dudgeon/count-fidget/procurement/q4/drill-report-Q4.txt

Drill report for click-counter-Q4.kicad_pcb
Created on 2026-09-24T20:55:30

Copper Layer Stackup:
    =============================================================
    L1 :  F.Cu                      front
    L2 :  B.Cu                      back

Drill file 'click-counter-Q4-PTH.drl' contains
    plated through holes:
    =============================================================
    T1  0.300mm  0.0118"  (79 holes))
    T2  0.600mm  0.0236"  (4 holes)  (with 4 slots)
    T3  1.020mm  0.0402"  (7 holes))
    T4  1.500mm  0.0591"  (4 holes))

    Total plated holes count 94

Drill file 'click-counter-Q4-NPTH.drl' contains
    unplated through holes:
    =============================================================
    T1  0.650mm  0.0256"  (2 holes))
    T2  2.200mm  0.0866"  (4 holes))
    T3  3.950mm  0.1555"  (2 holes))

    Total unplated holes count 8
