dudgeon/count-fidget/LOCAL_SESSION_PROMPT.md

Continue my Count Fidget project from https://github.com/dudgeon/count-fidget in this local session.

Clone/open the repo, read AGENTS.md, PROJECT.md and HANDOFF.md, then follow the handoff. It contains the product requirements, design files, decision history, vendor conversations, exact upload files and unresolved engineering issues. Do not restart or ask me to repeat the requirements.

First verify that you can actually control the local browser. Then complete the already-authorized website submissions to PCBWay and JLCPCB and obtain itemized quotes for 5 and 10 fully assembled/programmed/tested units, including the prepared rechargeable battery harness and delivery. Record real upload/submission evidence. Check existing replies and the old scheduled cloud follow-up to avoid duplicate actions.

Do not spend money, preorder chargeable parts or release manufacture until I approve a concrete order. The Q1 design is a quotation prototype; preserve the documented qualification gaps and keep moving on the work you can complete.
