dudgeon/count-fidget/docs/REVIEW-Q5-2026-09-25.md

# Q5 engineering review — 25 September 2026

**Start here for Q5.** Q5 is a coordinated revision of the frozen Q4 candidate. It resolves the ten findings filed from the Q4 simulation review ([issues #2–#9, #12, #13](https://github.com/dudgeon/count-fidget/issues?q=is%3Aissue)) and the owner's requests of 25 September:
- soft power on the COUNT key with automatic power-off;
- a battery gauge, low-battery warning and storage cut-off;
- charge status;
- a reachable hardware reset;
- new key logic (increment wins; reset needs a deliberate hold);
- a shrunk enclosure;
- a BOM of JLC inventory parts only.

Q1–Q4 files are unchanged.

The design is **locked** as of the evening of 25 September (see [Design lock](#design-lock--25-september-evening)). JLCPCB quoting was then authorized for two variants only:
- variant A: JLC does all SMT and the user solders the display;
- variant B: JLC assembles everything.

The result is in [JLC-QUOTE-Q5](../procurement/q5/JLC-QUOTE-Q5.md). No order, payment, allocation, manufacturing release or other-vendor contact is authorized. Everything here is design-file, host-model, emulator and CAD evidence. **Nothing has been built or measured.**

Related documents: [Q5 power design](q5-power-design.md), [Q5 firmware and home programming](q5-firmware.md), [enclosure and assembly](../mechanical/q5/README.md), [build workflow](build-and-verify.md#active-q5-engineering-workflow), [Q4 simulation review that raised the issues](REVIEW-Q4-simulation-2026-09-25.md).

## What Q5 is

- **Unchanged from Q4:**
  - STM32L072CBT6 with ROM USB DFU;
  - FM25V02A SPI FRAM with the same 96-slot journal (a Q4 FRAM image reads unchanged);
  - HS96L01W4S03 SPI OLED module;
  - BQ25185 charger, BQ29700 protector, TLV767 3.2 V rail;
  - two-layer 42 × 54 mm board and the same four mounting holes, now **1.6 mm** thick (required by the hot-swap sockets).
- **Parts count:** **95 references: 81 fitted (80 vendor SMT + DS1) and 14 PCB features**, 41 exact MPNs.
  - The key switches are no longer soldered. SW1/SW2 are vendor-placed MX hot-swap sockets, and the loose clicky switches K1/K2 press into them.
- **Home completion:**
  - variant A: 14 joints (the display header);
  - variant B: none (JLC fits DS1).
- **Offboard items:** reduced to the user-supplied LIR2032 cell.

## Fix order and why

Each fix was placed so that nothing done earlier had to be redone:

1. **Architecture/netlist decisions first** (#12, #13, #8, #5): power latch, cell holder + onboard NTC, battery sense, charger status, QOD. These change pins, so firmware and layout depend on them.
2. **Firmware** against the new pin contract:
   - boot capture gate (#2);
   - key semantics and DFU safety (#3 and the owner's reset rule);
   - option-byte provisioning (#6);
   - responsiveness (#7);
   - power-off, gauge and cut-off (#12, #9.4);
   - PVD wording (#9.1).
3. **Instruction-level emulation** of the actual ELF on a Q5 board model, before any layout work, so behavioural bugs were found cheaply. Four firmware defects were found and fixed here: the mV overflow, the label priority, the USB-during-LO cancel, and release-loop flapping.
4. **PCB placement, routing, ERC/DRC** once the netlist was final.
5. **Enclosure** from the final routed board (#4, pack-bay removal, keycaps, reset pinhole, shrink).
6. **Stock screen and exports** bound to the final model hash.
7. **Documents and issues.**

## Design lock — 25 September (evening)

Three independent reviews ran against the first Q5 candidate: hardware/DFM, firmware, and mechanical/quote. Their findings were fixed before the lock:

| Area | Finding | Fix |
|---|---|---|
| Latch | A short COUNT press could release U7 before PB2 took over; the power-on press could be lost | The reset handler drives PB2 first. C40 on SYS_ON bridges the gap (4.7 nF at the lock, 10 nF from 26 Sep: 9.9 ms). The boot scan captures edges. R38 isolates the VBUS path. Minimum press 10.5 ms typ / 16.3 ms allowance with 10 nF. Emulator B5/B6 |
| Firmware | After a DFU leave, ROM leftovers (VTOR, USB, SYSCFG) hung the app | `startup.c` detects leftovers and resets. Emulator D5 |
| Firmware | ADC read without VREFINT ready or LFMEN; option provisioning loop; key releases counted as activity | Fixed per [q5-firmware](q5-firmware.md) |
| Assembly | The two MX switches needed home through-hole soldering, and JLC has no stocked clicky 5-pin MX switch | **HanElectricity CPG151101S11-16 hot-swap sockets (C41430893)**, vendor SMT on the bottom. The clicky CPG151101D13 switches clip into the printed plate and press in. A soft-tactile JLC switch was rejected because the click is central per the user research. The sockets need a **1.6 mm** PCB |
| BOM cost | 10 generic passive/FET types were Extended parts ($3.07 feeder fee each) | Swapped to JLC Basic equivalents with the same value, package and rating (0.1 % dividers, 10 µF/2.2 µF and BAT54C unchanged): 25 Extended types remain |
| Silkscreen/DFM | Strokes < 0.15 mm, BT1 inner silk, BT1 paste, J1 shield ring | All raised to JLC minimums; BT1 +/− marks added |
| Enclosure | Keycap datum, screw engagement, boss clipping, USB rib | M2 × 6 self-tapping (C357360) with 3.4 mm engagement, keycaps re-datumed on the socket; body **47.2 × 59.2 × 16.8 mm** |

After the lock the whole chain was re-run on the final sources:
- placement and routing (deterministic Freerouting);
- fresh ERC/DRC/parity;
- the verifier and its corruption tests;
- stock screen and exports;
- enclosure;
- emulator and flasher tests.

The home flashing tool for macOS is `tools/clicker-flash/` (Claude skill `flash-clickers`). It is tested against a dfu-util emulator and against real dfu-util argument handling with no device attached. It has not been used on a physical board.

## Basic-part review — 26 September

Every JLC Extended part type adds a $3.07 feeder fee to each order. At the 2–5-board first-article quantity that was $77 of fixed cost, about $15–38 per board. The owner asked that every Extended part earn its place.

Nine types moved to JLC Basic parts; the circuit was re-derived where the value changed:

| Part | Was (Extended) | Now (Basic) | Effect |
|---|---|---|---|
| R4 ISET | 16.5k | 18k (C25810) | Charge current 300/R = **16.7 mA** (was 18.2 mA); 0.37C of a 45 mAh cell. Termination 1.67 mA, still < 0.05C |
| R10/R11/R12/R13 temperature window | 57.6k/115k/24.3k/16.2k | **56k/82k/18k/12k** | Nominal B3380 NTC enable window **7.26–35.83 °C** (was 7.49–35.92 °C) |
| R32 memory-rail resistor | 68 Ω | 75 Ω (C4275) | 10 % slower VFRAM ramps (more margin on the FM25V02A slew minima); drop at 3 mA 0.225 V, VFRAM ≥ 2.93 V |
| Q1/Q2 protection FETs | DMN2056U-13 | **AO3400A** (C20917) | Same SOT-23 G/S/D; 30 V; ≤ 48 mΩ at VGS 2.5 V, so the 24.8 mA OCD bound is unchanged. LCSC pin names checked |
| C1/C3/C5 | Murata 2.2 µF 25 V X7R | Samsung CL21A225KBQNNNE 2.2 µF **50 V** X5R | Same 0805 land; more effective capacitance at 5 V |
| C2/C6/C30 | Murata 10 µF 25 V X5R | Murata GRM21BR61H106KE43L 10 µF **50 V** X5R | Same 0805 land; more effective capacitance. C30 ≥ 6.8 µF remains a first-article measurement. Slightly more SYS capacitance at cold insertion; that counterexample was already retained, and USB-first insertion still applies |

Result: **16 Extended types (was 25), about $28 less per order.** The re-verified chain passes: ERC, fresh DRC/parity on the unchanged routing, stock 42/42, exports, the JLC footprint fit (no mirror or pad-order error) and the power and latch checks.

The 16 remaining Extended types, and why each stays (no Basic equivalent without a redesign):

| Part | Why it stays |
|---|---|
| STM32L072CBT6 | MCU with ROM USB DFU, the home-flashing path |
| FM25V02A FRAM | Count journal with unlimited endurance and instant, brownout-safe writes |
| BQ25185 | Li-ion charger with power path and status pins |
| BQ29700 | Li-ion cell protection (safety) |
| TLV76701 LDO | Adjustable 3.2 V rail kept below the 3.3 V logic and FRAM limits |
| 150k 0.1 % (R30/R36/R37), 49.9k 0.1 % (R31) | The LDO set point and the 0.26 % ADC margin that separates USB from a full cell |
| TPS22917 (U6/U7) | Soft-power latch and display power switch |
| TLV7012 | Charge-temperature window comparator |
| NCP18XH103F03RB NTC | No Basic 10k NTC; the window is designed around its B3380 curve |
| R9 3.3 Ω | Sets the ~25 mA protection trip; no Basic 3.3 Ω exists, and 2.2/4.7 Ω would move the trip to ~37 or ~17 mA |
| BAT54C | Power-latch OR diode; replacing it with two Basic diodes would need re-layout |
| USBLC6-2SC6 | USB ESD protection; no Basic equivalent |
| USB4105 USB-C | The enclosure is designed around it |
| CR2032-BS-6-1 holder, CPG151101S11 hot-swap sockets | Unique mechanical parts |

## First-order de-risking — 26 September

Before the first paid order, the owner asked for more certainty. Three independent checks ran on the locked design:

| Check | Result | Evidence |
|---|---|---|
| **Datasheet pinout audit** of every active and polarised part (MCU pins and SPI alternate functions, charger, LDO, protector, comparator, switches, FRAM, ESD, diodes, FETs, USB-C, holder, sockets, display module) | **No pin-assignment errors.** The standard footprints are pad-for-pad identical to the official KiCad library, and the custom ones match the vendor drawings. | [pinout audit](first-order-derisk/pinout-audit-2026-09-26.md) |
| **Footprints against JLC's own EasyEDA footprints** (all 43 LCSC parts) | **No pad-order or mirror errors.** The raw KiCad CPL, however, would show ~15 polarised parts with the wrong pin 1 in JLC's preview, and SW1/SW2, J1 and DS1 offset. JLC-corrected CPLs were generated, and a preview checklist is in [JLC-QUOTE-Q5](../procurement/q5/JLC-QUOTE-Q5.md). | [footprint check](../scripts/q5_jlc_footprint_check/REPORT.md) |
| **Dead-on-arrival review** of the power-up paths, back-feeding, programming and latch failure modes | **No defect likely to leave a board dead or unrecoverable.** USB-only power-up, DFU entry (crystal-less, BOOT0 only) and the SWD fallback pads are confirmed. | this section |
| **Latch transient** (behavioural ngspice, bouncing contacts, 54 corners) | 120/120 bouncing presses latched. The worst-case minimum press is 14.5 ms with 10 nF (20.0 ms with 4.7 nF). USB alone turns the board on at every corner. | [q5-latch-spice](../simulation/q5-latch-spice/README.md) |

The findings led to these changes, all re-verified through the full chain: model, ERC, re-route, DRC/parity, verifier corruptions, emulator, stock, exports and enclosure.
- **R39 1k + C9:** filters U5's supply. U5 is a TLV7012 with a 6 V absolute maximum, and it was on raw VBUS, exposed to USB hot-plug ringing.
- **C40 4.7 → 10 nF:** doubles the bounce bridge and cuts the minimum latch press to 10.5 ms typical.
- **JLC-corrected placement files** plus a preview checklist.
- **Flasher and skill:** a clicker left in DFU mode must be reset with the pinhole *before* unplugging. The ROM's D+ pull-up back-feeds VBUS through the USBLC6 and holds the latch on, draining the cell.
- **Doc corrections:** the SSD1315 VBAT absolute maximum is 6 V (4.5 V is the recommended maximum), and the BQ25185 battery UVLO (~3.0 V) comes before the protector's 2.8 V.

Accepted and documented rather than changed:
- **Display module at 3.15–3.26 V.** The module's external input is specified at 3–5 V. The 3.5–4.2 V figure is the controller's internal pump input, and the module's internal power tree is undocumented. First-article test E1.
- **STAT pull-ups.** The MCU's internal ~40 kΩ is outside TI's 1–20 kΩ recommendation, but it is adequate for a static status read.
- **VDDA.** It has 100 nF only; ST also recommends 1 µF. The 10 µF bulk capacitor sits on the same rail.
- **No watchdog.** Firmware can be updated after assembly.

Recovery routes if something is wrong on the first boards:
- **SWD:** TP3 SWDIO, TP4 SWCLK, TP11 NRST and TP1/TP2 accept a standard ST-Link.
- **Latch control fails:** bridging TP13 (SYS_ON) to TP6 (SYS) holds the board on.
- **Stuck in DFU:** the pinhole resets it.

## Resolution by issue

| Issue | Q5 resolution | Evidence | Remaining physical gate |
|---|---|---|---|
| [#2](https://github.com/dudgeon/count-fidget/issues/2) boot ERR after journal wrap | Button capture starts only after the journal load. Faster boot: FLASH latency 0, CS guard 110 loops, nibble CRC-32 table. | Emulated boot drains the queue at 207 ms with all 96 slots valid; no sample dropped; host CRC equivalence over 20,000 records | Boot timing on silicon |
| [#3](https://github.com/dudgeon/count-fidget/issues/3) DFU entry zeroes count | A reset commits only on **release** after a completed ≥ 2 s hold. A key held at MCU start is a level, not a press. On battery, NRST is a power cycle. | Emulator D1–D4 preserve the count in both DFU entry orders | Real DFU enumeration |
| Owner key rule | Both keys → **increment wins**, and the reset is cancelled. Reset needs a **2 s hold** (RST shown) and a release before 10 s. | 826 host key-hold cases; emulator K2, K3, K5–K7 | Contact bounce on real switches |
| [#4](https://github.com/dudgeon/count-fidget/issues/4) USB plug can't mate | 13.4 × 7.2 mm opening on the receptacle axis, cut through to the receptacle face; checked against a USB-IF maximum overmold | Fit report: USB mouth 2.0 mm from outer wall, no intersections | Real cables, both orientations |
| [#5](https://github.com/dudgeon/count-fidget/issues/5) 2–3 week battery life | Solved by #12: everything below SYS is off when idle; the regulator is kept | Off current 8.0 µA typ; emulated life 150–169 days on a shelf, 81–91 light, 42–48 moderate, 14–16 heavy | Measured off current and runtime |
| [#6](https://github.com/dudgeon/count-fidget/issues/6) blank board with factory option bytes | Firmware programs USER 0x807C once (BOR_LEV 0xC only; never RDP) and reloads. Any other mismatch shows **OPT**. | Emulator O1 (factory 0x8070 → provision → counts), O2 (OPT) | Option programming on silicon |
| [#7](https://github.com/dudgeon/count-fidget/issues/7) slow display | First frame in GDDRAM before AFh; partial redraw; 31-byte packets; no-divide glyph renderer; module powered during the journal scan | Press to digits 60–66 ms (Q4 200–225); USB Stop wake 0.34 s (Q4 0.77); off → lit 0.45 s | Optical response |
| [#8](https://github.com/dudgeon/count-fidget/issues/8) OLED supply | U6 QOD unconnected (SSD1315 §6.9.2). The display now runs only on a regulated ≥ 3.151 V rail because the 3.35 V cut-off precedes dropout. The supply choice is explained in the power document. | Netlist/ERC; emulator hard-reset cases note the floating supply | Module power tree, VBAT/pump/current, 200 × NRST |
| [#9](https://github.com/dudgeon/count-fidget/issues/9) minor findings | (1) PVD5 documented as best-effort only. (2) USB-first insertion cited to SLUSBU9I §8.4.1 in docs and assembly. (3) Cold-insertion counterexample retained; the latch keeps SYS_LOAD off at insertion. (4) **LO** label plus a 3.35 V cut-off, so there is no blind counting. | Emulator L1–L4; `simulation/q5-power` | Insertion on real cells; first-connection behaviour |
| [#12](https://github.com/dudgeon/count-fidget/issues/12) soft power | COUNT/SW1 switches SYS onto U7 ON; PB2 holds it; VBUS holds it via D4. The power-on press counts. 30 s auto-off on battery; Stop fallback with USB. | Emulator B1–B5, U1–U5, C4, H1/H2; latch press ≥ 10.5 ms typ / 16.3 ms allowance (C40 10 nF); ngspice 120/120 bouncing presses latched; inrush below the 24.8 mA minimum OCD over temperature | Latch timing with a bouncing contact; release behaviour |
| [#13](https://github.com/dudgeon/count-fidget/issues/13) JLC-inventory BOM | Pack/harness → vendor-soldered BT1 holder + onboard TH1. Keycaps printed. U5 moved to TLV7012DDFR (881 stock). All 41 MPNs pass a 10-board + spares screen. | `procurement/q5/stock.json`; offboard CSV = LIR2032 only | Signed-in JLC parts match for variants A/B ([estimate](../procurement/q5/JLC-QUOTE-Q5.md)) |

New in Q5 beyond the issues:
- **Charge status:** CHG while charging, full gauge when done, BAT on fault.
- **4-bar gauge.**
- **Reset pinhole:** a bottom opening reaches SW3 (NRST).

## Key and display behaviour (user-visible summary)

- **COUNT** (+ keycap) adds one; from off it powers on and that press counts. Held keys never repeat.
- **RESET** (○ keycap): hold 2 s until **RST** appears, then release (within 10 s) to zero. Pressing COUNT at any time cancels it.
- **Top-right:** 4-bar battery gauge. **LO** below ~3.55 V; below 3.35 V the count is saved and the board turns off. **CHG** while charging.
- **Auto-off:** 30 s after the last key on battery. With USB, the display sleeps and the MCU stops.
- **Label priority:** OPT > RST > ERR > MAX > LO > CHG/BAT.

## Validation record

| Scope | Evidence |
|---|---|
| Native schematic/PCB | Fresh KiCad 10.0.6: **ERC 0, DRC 0 violations, 0 unconnected, 0 parity**; 95 refs, 268 connected pins, 22 explicit NC pins ([binding](../verification/q5-validation.json)). 1,034 tracks, 121 vias, two GND pours, re-planned stitching vias ([gnd-stitch.json](../electronics/q5/gnd-stitch.json)); no same-net via closer than 0.1 mm to a land |
| Verifier corruption rejection | [42 of 42 rejected](../verification/q5-negative-tests.json) after a clean native baseline |
| Target build | Arm GNU 14.3.Rel1; 10,652 loaded bytes, 2,432 static RAM bytes, Bank 1 only, EEPROM and option bytes excluded ([manifest](../firmware/q5-stm32/build/build-manifest.json)); 13 image corruptions rejected ([image checks](../verification/q5-firmware-image-checks.json)) |
| Portable firmware models | [Full suite](../verification/q5-firmware-tests.json): 1,179,648 torn-word reboots, 256 bit corruptions, 7,072 button waveforms, 826 key-hold cases, 2,295 queue/storage schedules, 200 recovery interleavings, 350 FRAM faults, OLED transport faults at 80 positions, 1,527,742 rail corners, 1,301 battery-policy readings. [UBSan run](../verification/q5-firmware-sanitized-tests.json) (gcc; clang's UBSan runtime is not installed here) |
| Instruction-level emulation | 37 scenario records on the final ELF (SHA-256 below), **0 expectation failures** ([results](../simulation/q5-firmware-emulation/results/scenarios.json)); [energy model](../simulation/q5-firmware-emulation/results/energy-model.json) |
| Bounded power calculations | [result.json](../simulation/q5-power/result.json): latch, inrush, off current, ADC separation, cold insertion (counterexample retained), storage |
| Enclosure | [Fit report](../mechanical/q5/fit-report.json): five valid, manifold parts; zero static intersections; 162 poses / 18,387 sampled path tests with zero collisions; renders inspected |
| Stock and exports | 41/41 exact MPNs pass; lowest stock DMN2056U-13 189, HS96L01W4S03 524, TLV7012DDFR 881 (read-only public catalogue, unallocated). Exports in [procurement/q5](../procurement/q5/REVIEW-EXPORTS-Q5.md): variant A BOM/CPL (80 SMT rows) and variant B BOM/CPL (+ DS1, DS1H THT); loose parts; LIR2032 offboard |

- PCB SHA-256: `e78629ed361ff9f38c8ead58770e2dd60fc865461600456b503f6015345428df`.
- Firmware ELF SHA-256: `bb5a4a38aeeb41213e5f46c07e4a361e69b22f9b96742ebbff875b6083f58b03`.
- Gerber ZIP: 12 members, 134,522 bytes, SHA-256 `f9b9afe4ead8ebe9c9f7066926ef95a16f03e42750d92ad6f939462d12864230`.
- This ZIP was uploaded to JLC's public quote page for a price only. No RFQ was submitted, no cart was saved and nothing was ordered.

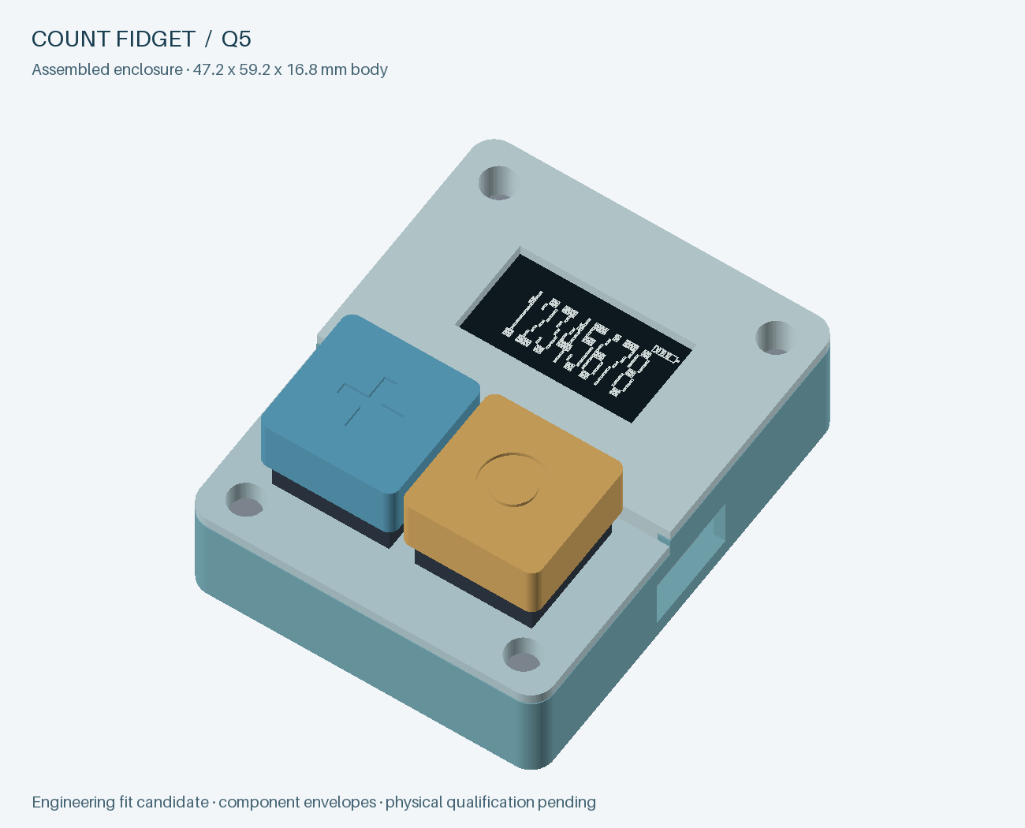
[picture p1: mechanical/q5/assembled-Q5.png]
Q5 CAD rendering


## Physical gates before an order can be released

The Q4 gates still apply: USB/target execution, supply/interface behaviour, charger/protector/temperature, count and display reliability, assembly and enclosure. Q5 adds or changes these:

1. **Power latch:** minimum press to latch with a real bouncing MX contact; clean U7 turn-off on PB2 release; USB unplug during Stop; the NRST power cycle on battery.
2. **Battery sense and status:** ADC accuracy through the 75 kΩ divider source; gauge thresholds against a real LIR2032 discharge under display load; STAT1/STAT2 behaviour in every charger state; measured ~8 µA off current.
3. **Cell and holder:** holder contact resistance and retention; insertion with USB present (BQ2970 first connection); the retained cold-insertion counterexample on real cells; TH1 thermal coupling to the cell.
4. **Display supply (#8):** module power tree; VBAT, pump, readability and current at 3.15–3.26 V; 200 × NRST with the display on.
5. **Enclosure:** real USB-C cables in both orientations; printed keycap cross-socket fit and travel; pinhole access to SW3; load supports; cell replacement.
6. **Process:** BT1, J1 and hot-swap socket solder inspection; variant B acceptance of the stacked THT display. The PCB price was observed on JLC's quote page, and PCBA is estimated from published fees; the parts-matched PCBA quote needs the owner's signed-in upload ([JLC-QUOTE-Q5](../procurement/q5/JLC-QUOTE-Q5.md)).

The full first-article procedure is [q5-first-article-test-plan.md](q5-first-article-test-plan.md).

**No whole-board simulation or physical working unit is claimed.** The evidence above supports building a first article when the owner authorises it. It does not replace these measurements.
