dudgeon/count-fidget/docs/q2-display-selection.md

# Q2 display recommendation

**Superseded by the user's explicit replacement requirement on 15 September 2026.** This is the historical Q2 decision. Continue with [Q3 display replacement](q3-display-selection.md); retaining DE188 did not satisfy support at both assemblers. Submitted Q2 files remain historical evidence.

Reviewed **2026-09-15**. **Retain the exact 3 V Display Elektronik DE188 for the corrected Q2 engineering baseline.** Correct its bias capacitors, frame timing and footprint; obtain an assembler's actual sourcing quotation before deciding to replace it. This is an engineering recommendation, not a purchasing or production approval.

The original eight digits, 35 × 13 mm envelope and 2–4-month runtime estimate were implementation assumptions, not user requirements. The user explicitly says the display choice was arbitrary. Even with those assumptions relaxed, the passive alternatives below do not have verified purchasable JLCPCB inventory. Reducing to four digits solely to resolve JLC sourcing therefore has no demonstrated benefit. The OLED and memory-LCD leads in [the earlier comparison](display-options-Q2.md) remain unqualified.

## Three concrete sourcing paths

All inventory and prices below are **indexed official distributor-page observations**, not live reservations, supplier commitments or complete assembly quotes. The stated crawl ages are part of the evidence. Prices are USD per component before assembly, fixtures, project freight and other commercial scope.

| Exact part | External sourcing evidence | Electrical/mechanical fit and assembly | Decision |
|---|---|---|---|
| **Display Elektronik DE 188-RU-30/7,5 (3 Volt)**; TME ordering name **DE 188-RU-30/7,5/V (3 VOLT)**, TME code **DE188-RU-30/7.5-3** | [TME](https://www.tme.com/us/en-us/details/de188-ru-30_7.5-3/lcd-digital-displays/display-elektronik/de-188-ru-30-7-5-v-3-volt/) reports **288**, MOQ/multiple **1**, **$3.60 single/$2.80 at ten**. Opened retrieval was crawled **five months ago**: useful source identity, weak evidence of today's quantity. No delivery date was obtained. | Reflective eight-digit glass, **34.9 × 13 mm**, 3 V AC, 1/4 multiplex, 20 leads. Existing MCU architecture and segment mapping remain useful. Through-hole assembly and glass support need approval. Use the exact **3 V Rev4 drawing**, not the 4 V variant. | **Preferred.** Least redesign while retaining the low-power architecture. TME is a sourcing lead for vendor confirmation, not an accepted PCBWay supply plan. |
| **Lumex LCD-S401M16KR**, JLC/LCSC **C17355221** | [DigiKey](https://www.digikey.com/en/products/detail/lumex-opto-components-inc/LCD-S401M16KR/7364561) reports **6,108**, quantity **1**, **$2.07 single/$1.484 at ten**, crawled **the previous day**. Listed manufacturer standard lead time **18 weeks** is not a quoted ship time for those stocked units. | [Manufacturer drawing](https://www.lumex.com/datasheet/files/LCD-S401M16KR.pdf): four reflective digits, **20.32 × 10.16 × 2.8 mm**, **3 V AC, 1/4 duty, 1/3 bias**, 12 leads. [JLC listing](https://jlcpcb.com/partdetail/Lumex-LCDS401M16KR/C17355221) identifies wave soldering but exposes no inventory figure; [LCSC](https://www.lcsc.com/product-image/C17355221.html) reports zero. | Credible smaller external-source fallback. Requires a new footprint, wiring/segment map, enclosure and count presentation beyond four digits. No demonstrated JLC inventory advantage. |
| **Varitronix VIM-878-DP-RC-S-LV**, JLC **C17231725** | [DigiKey](https://www.digikey.com/en/products/detail/varitronix/VIM-878-DP-RC-S-LV/1118605) reports **1,381**, quantity **1**, **$4.80 single/$3.556 at ten**, crawled **two weeks ago**. Its **20-week** manufacturer lead time likewise does not establish stocked-order delivery. | Eight 14-segment characters, reflective, **52 × 22 × 2.8 mm**, listed **3.3 V**. [Exact manufacturer drawing hosted by DigiKey](https://mm.digikey.com/Volume0/opasdata/d220001/medias/docus/693/VIM-878.pdf). [JLC](https://jlcpcb.com/partdetail/18360830-VIM_878_DP_RC_SLV/C17231725) shows **stock 0**, wave soldering and a required fixture. Exact MCU pin/drive compatibility and optical response have not been qualified. | Externally stocked eight-digit fallback, but its 52 mm glass exceeds the current 42 mm board width. Larger mechanical redesign and drive review bring no demonstrated JLC sourcing benefit. |

No assembler has provided a firm lead time or complete price for any of these sourcing paths. JLCPCB's representative suggested Global Sourcing preorder for DE188 and reported no stocked alternative to the originally narrow display request; see [vendor status](../procurement/vendor-status.md). That statement is not an exhaustive catalog search. Paid preorder remains unauthorized. PCBWay external sourcing still requires its acceptance, quantity, lead time and itemized price.

## Necessary DE188 work and remaining risk

1. **Bias hardware:** add the three nominal **100 nF** R13/R23/R33-to-ground reservoirs at MCU pins **7/8/9**. Retain the existing nominal 100 nF pump capacitor unless further review changes it. [TI datasheet §8.12.8.1](https://www.ti.com/lit/ds/symlink/msp430fr4133.pdf) and [family guide Figure 17-9](https://www.ti.com/lit/ug/slau445i/slau445i.pdf) support this correction.
2. **Timing:** use the separately verified **32 Hz** candidate. Its calculated REFO-tolerance range **30.88–33.12 Hz** fits the MCU and exact display recommendations. This does not measure the physical waveform or optical response.
3. **Footprint:** the [DE188 Rev4 drawing, p3](https://display-elektronik.de/filter/DE188-RU-30_75_3V.pdf) implies nominal **13.0 mm** lead-row centers, versus Q1's 13.5 mm. Confirm the interpretation and lead/hole tolerance stack; do not blindly shrink the existing drills. See [LCD audit](review-lcd-firmware-Q2.md).
4. **Response:** Rev4 p4 lists **440 ms total turn-on plus turn-off response**. That remains a meaningful fast-click visibility concern; changing frame frequency does not establish a faster glass response. The Lumex drawing does not supply a qualified optical-response comparison. Verify actual rapid counting, contrast, DC balance, temperature and current on a first article before accepting the display experience.

[NXP AN12579 §4](https://www.nxp.com/docs/en/application-note/AN12579.pdf) demonstrates the Lumex display in an active low-power development-board configuration at 7 µA. This supports a passive-LCD direction; it is not a bare-display specification, Count Fidget current measurement or runtime promise.

The separate Q2 native design implements the retained-display corrections and has its own verification and quote files. Q2 files are now uploaded to both vendors: PCBWay has a submission under review, and JLCPCB has a saved draft blocked at the unmatched required DE188 and stock shortages. Q1 remains historical and on engineering hold. See the [vendor ledger](../procurement/vendor-status.md) for current evidence. Charger, thermal, cell/protection, physical mechanical fit, target tests and other [release gaps](open-issues.md) remain open. File checks and a quote do not authorize spending or manufacture; concrete order approval remains required.
