dudgeon/count-fidget/docs/REVIEW-Q3-2026-09-22.md

# Q3 independent-review entry point — 22 September 2026

## Decision and boundaries

Commit the coordinated **two-layer OLED Q3 candidate** for another agent to review. Retain the exact circuit and part identities: fresh read-only research establishes a stock source for every fitted PCB MPN without speculative substitutions. This is a review candidate, **not a demonstrated working device or manufacturing release**. The new review strengthens the software evidence and identifies concrete conditional electrical failure scenarios; those scenarios remain open.

**No new quote submissions, uploads, draft changes or vendor messages are authorized.** The user paused them pending a separate explicit instruction. No purchases, paid preorders or manufacturing release occurred. The September15 RFQ is a frozen historical snapshot, not a new submission or a package containing this September22 review.

## What another reviewer should examine first

1. [Fresh hardware review and proposed remedies](review-Q3-2026-09-22-hardware.md) (a self-review by the power/layout author, alongside the separate September15 independent audit): I²C acknowledgement/rise-time margin, battery-insertion surge and OLED power budget. Challenge the model assumptions; do not treat its grid as guaranteed component limits.
2. [Fresh firmware adversary](review-Q3-2026-09-22-firmware.md): bounded tests execute the actual portable production modules, including torn writes and display errors. The MCU peripherals and analog supply are outside that model.
3. [Current exact-part inventory](../procurement/q3/stock-recheck-2026-09-22.json):40 MPNs available in JLC inventory and3 exact MPNs with independent distributor stock. This is not an all-JLC-stocked turnkey build.
4. [Home completion and cost options](home-completion-Q3-2026-09-22.md): shared programmer, optional home switches, USB programming tradeoffs and actual limits on claimed savings.
5. [Open issues](open-issues.md), [power circuit](q3-power-design.md), [original hardware review](review-hardware-Q3.md), [original firmware review](review-firmware-Q3.md) and [mechanical review](review-mechanical-Q3.md).

The board, schematic and all70 fitted references are under `electronics/q3/` and `procurement/q3/`. Firmware is `firmware/q3-oled/`. The MCU remains MSP430FR4133IG48R. The exact display is X087-2832TSWIG02-H14/C18723015, with a TPS63900 supply and gated pump input. Q1/Q2 remain separate historical revisions.

## Fresh stock result

Observed23:48–23:58 UTC on September22. All43 MPN records were checked against the actual70-reference design and their required ten-board quantities before attrition. Stock is neither reserved nor supplier allocation.

| Scope | Observed result | Limit |
|---|---|---|
| OLED C18723015 | JLC stock1,065; available1,052; minimum1 | Exact FPC assembly process still needs approval |
|40 of43 unique PCB MPNs | JLC explicitly showed sufficient available quantity for10 boards before attrition | MCU and comparator quantities are relatively tight; check allocation/attrition later |
|J1 USB4105-GF-A | JLC preorder/ordering restriction; LCSC out of stock; DigiKey129,457 exact parts | Distributor sourcing/consignment is not accepted vendor scope yet |
|Q1/Q2/Q6 DMN2056U-7 | JLC preorder/ordering restriction; LCSC out of stock; DigiKey57,542 exact parts | Need three per board plus eventual attrition |
|R13 RC0603FR-0716K2L | JLC preorder/ordering restriction; LCSC out of stock; DigiKey262,066 exact parts | Retain exact16.2k1% thermal-network identity |

Sources, observation times, minimum quantities and exact reference mappings are in the inventory record. DigiKey's cut-tape tiers start at1 for these three identities. No component was purchased or omitted. This establishes an exact-part sourcing path, not full support by both assembly vendors. The offboard custom welded cell/NTC pack remains a separate unapproved assembly; the43-MPN claim does not include it.

## Verification and its limits

| Check | Result | What it establishes |
|---|---|---|
|Q3 model/schematic/PCB/BOM/CPL and source-bound native evidence | Pass;82 references/features,218 connected pins,50 explicit NC,70 fitted components | Unchanged source agreement; existing native electrical/connectivity/parity results remain valid. One exact disclosed J1/SW2 courtyard projection remains |
|Negative checks |62 deliberately corrupted cases rejected on September22 | Checker rejects the tested identity, topology, geometry, report and provenance corruption |
|Firmware provenance | Source/output manifest passes; frozen ELF/HEX unchanged | Candidate images correspond to the recorded source/toolchain; original September15 independent exact rebuild remains evidence |
|New deterministic software model |2,359,296 torn-word cases;65,536 marker patterns;65,665 queue schedules/capacity cases;7,350 button waveforms;24 recovery-cut prefixes;5,441 OLED fault/sleep schedules pass | Bounded functional behavior of actual portable production code; not exhaustive states or electrical power-cut simulation |
|New hardware corner analysis | Conditional I²C and insertion-current counterexamples reproduced; RC result independently crosschecked numerically | Shows missing electrical guarantees. **Not a hardware pass** |
|Historical archive preservation |152 RFQ members match manifest and CRC; Q1/Q2 provenance checks pass | Preserved submitted/historical evidence |
|Mechanics | Existing source-bound four-part CAD result: valid solids/manifold meshes, zero modeled intersections | Simplified geometry/assembly sampling, not actual printing, material, harness or retention qualification |

No new native KiCad run was needed for this continuation because the final board/circuit and its bound inputs remain unchanged. The September22 binding recheck must not be described as newly executed native DRC/ERC. No new production-code bug was confirmed by the fresh bounded firmware tests.

### Concrete unresolved electrical questions

- **I²C:** the selected4.7k pull-ups require more sink current than the display's100µA output-low test establishes. A hypothetical6kΩ sink meets that table at100µA yet gives about1.68V acknowledgement with4.7k at3V, outside guaranteed MCU low recognition. It is a specification-consistent counterexample, not a measured OLED resistance. Weaker pull-ups alone do not establish compliance with the300ns rise limit and unknown bus capacitance.
- **Battery insertion:** a4.2V,20µF effective SYS,3.3Ω sense plus1Ω other-series-resistance model exceeds0.4V at the protector sense for about179.45µs, longer than its125µs minimum short-circuit delay. Actual cell impedance, capacitance, charger/protector gate slew and recovery are not established. TPS63900's10mA average input setting does not limit charging its input capacitor.
- **OLED operating budget:** the converter limit has no guaranteed min/max setting bound and sparse pixel current is unmeasured. Rail droop, pump startup and readability require proof under the intended load; a nominal efficiency calculation is not qualification.

Retain the cell/protection threshold,18.2mA charge stability, installed temperature sensing/fault response, capacitor effective values, sudden VDD collapse/FRAM, battery pack, actual assembly and runtime/mass gates. The firmware cannot preserve a newly detected volatile input-history gap if power disappears before its first marker write. The detailed reviews identify practical test and redesign branches; do not silently close those issues.

## Reproduce the review

From the repository root:

```sh
python3 scripts/verify_project.py
python3 scripts/verify_q3.py
python3 scripts/build_firmware_q3.py --verify-only
python3 scripts/test_verify_q3.py --full --bound
python3 scripts/test_q3_behavior_model.py
python3 scripts/analyze_q3_hardware_corners_20260922.py
```

The new software model needs a C11 host compiler; its result records the compiler, flags and input hashes. Existing negative checks use `/private/tmp` and need that scratch path on non-macOS hosts. See [build instructions](build-and-verify.md) for native tools if the engineering inputs change. Reusing an old binding after changing a bound input must fail.

Saved new evidence: `verification/q3-behavior-model-2026-09-22.json`, `verification/q3-hardware-corners-2026-09-22.json`, and `verification/q3-negative-recheck-2026-09-22.json`.

## Cost and USB programming decision

Two layers are already implemented. Retain one shared Spy-Bi-Wire programmer as the simplest current home-flashing path. Home soldering of the two switches is permissible if the actual savings justify it, but the observed manual-labor lines total only$5.06 per five-unit batch and include other work; the full$16.42 fixture is not necessarily avoidable. No savings quote is implied.

USB-C currently charges only. MSP430FR4133 has no native USB. Adding a USB-to-UART bridge would require bootloader-entry wiring and resolution of P1.0/P1.1 sharing with the buttons; a wrong bootloader password can erase information FRAM and the saved count. A native-USB MCU is a larger board/firmware/power redesign. The user's question does not select either change. Detailed constraints and primary references are in the firmware and home-completion notes.

The September15 JLC five-unit automatic total$255.86 and separate$3.28 depaneling remain historical incomplete pricing. No ten-unit Q3 total or complete delivered quote exists. Later email replies were read: JLC recognizes the OLED as an assembly component and said its wave-solder category appeared incorrect, referring it for correction; PCBWay requests one settled revision and warns that calculator prices are not final. No reply was sent.

## Rendering and immutable identities

[Actual assembled CAD rendering](../mechanical/q3/assembled-Q3.png), [STEP model](../mechanical/q3/enclosure-Q3.step).

- Board SHA-256: `b33b1e1d0c9e4d58c5642fc3f63faaa4e190092601f26103376537a5b12621fd`.
- Application HEX SHA-256: `b19f9e62fe9833ebb61fa75e94a7adef5664e51c7bcb7ffaa619a7c00bf910bf`.
- Historical September15 RFQ SHA-256: `4626d8ba64ef67d9bf5265399d6f6bf8e0d4ce9dda87d3656b5e5579aecef5ba` (4,031,548 bytes).

Next: independent review of this committed candidate, especially the three electrical questions and actual sourcing/assembly path. Resolve them as one coordinated revision before the user considers authorizing another quote. Do not restart the requirements interview or turn review completion into manufacturing approval.
