dudgeon/count-fidget/procurement/JLCPCB-IMPORT-ADAPTER-Q1.md

# JLCPCB Q1 import adapter

Prepared 2026-09-15 01:50:59 UTC. Quotation only; no design or manufacturing release.

## Observed import failure

During the local JLCPCB BOM import, the matching screen used descriptive Comment values such as COUNT and RESET and generic capacitor descriptions instead of the supplied Manufacturer Part Number column. This produced incorrect component matches. The earlier vendor screenshot also matched SW2 to E-Switch TL1220S1BBSG-RESET (C5798268), whereas the specified switch is Cherry MX1A-E1NW. Do not accept these automatic substitutions.

A first adapter import recognized the explicit catalog codes but still displayed the old descriptive values, including an incorrect LED match for R7 from the description 330. The importer appears to choose the last header containing Comment. The preserved-description header is therefore Source Label, with no Comment, Description or Value substring. This is an observed parser diagnosis, not a claim of successful matching.

The subsequent Source Label reimport displayed the exact MPN Comment values. This confirms the field-interpretation fix, while exact component matching and stock review remain unfinished. In particular, Q3 was still automatically mapped to a different manufacturer's part; U3 and DS1 remained unmatched. No complete quote resulted from this import.

## Adapter transformation

Use `BOM-JLCPCB-Q1.csv` with the unchanged `CPL-JLCPCB-Q1.csv` for this importer. It preserves every source row, row order and column. The only modified source field is Comment, set to the exact Manufacturer Part Number. The prior descriptive Comment is preserved in the appended Source Label column. The appended LCSC Part # column contains the verified exact catalog codes below for 11 references; all other code cells are blank.

`BOM-PCBA-Q1.csv` remains the controlling PCB BOM. The source BOM, full commercial BOM, CPL, Gerbers, firmware, electrical design and RFQ ZIP are unchanged. This adapter is a separately uploaded supplement and is not yet included in the RFQ archive.
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
