dudgeon/count-fidget/mechanical/exploded-cad.png

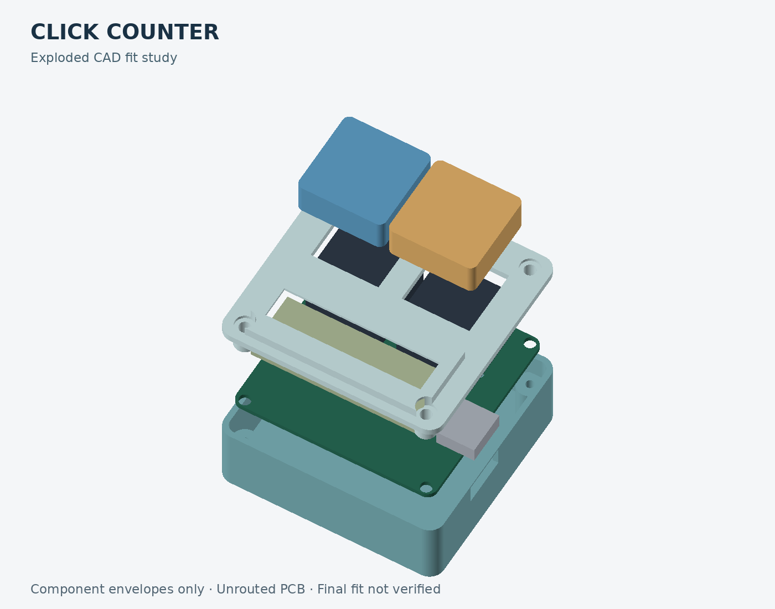
mechanical/exploded-cad.png
