dudgeon/count-fidget/mechanical/q2/battery-bay-Q2.png

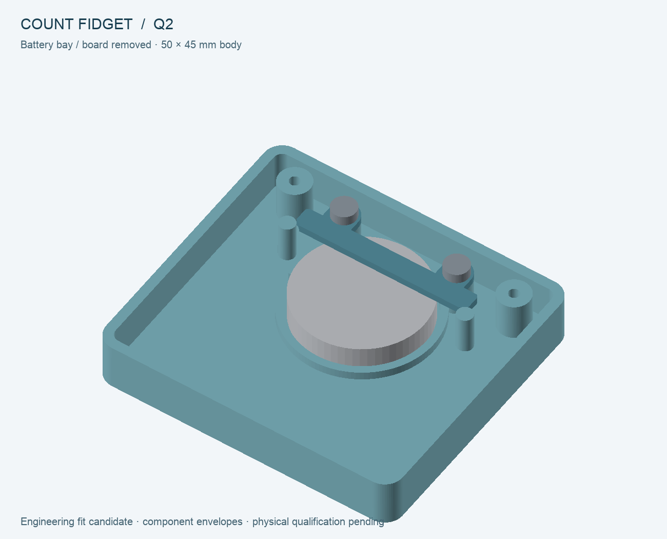
mechanical/q2/battery-bay-Q2.png
