dudgeon/count-fidget/mechanical/q2/exploded-Q2.png

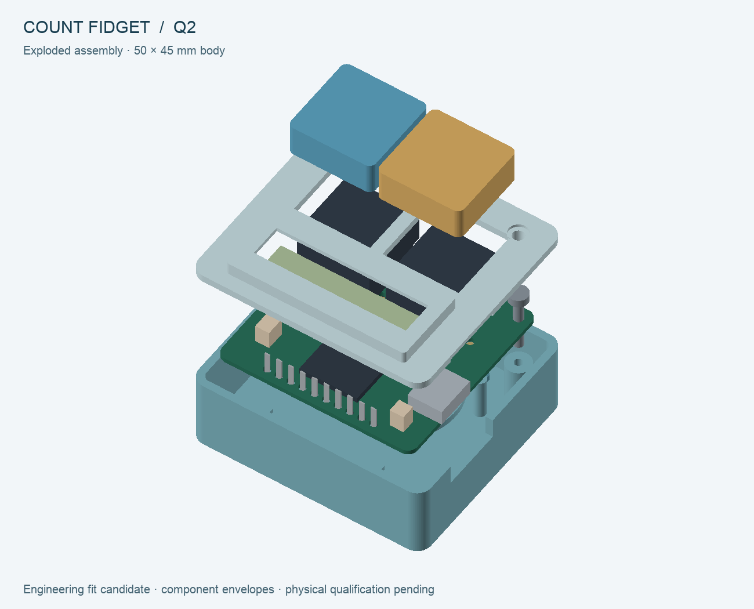
mechanical/q2/exploded-Q2.png
