dudgeon/count-fidget/mechanical/q2/interior-Q2.png

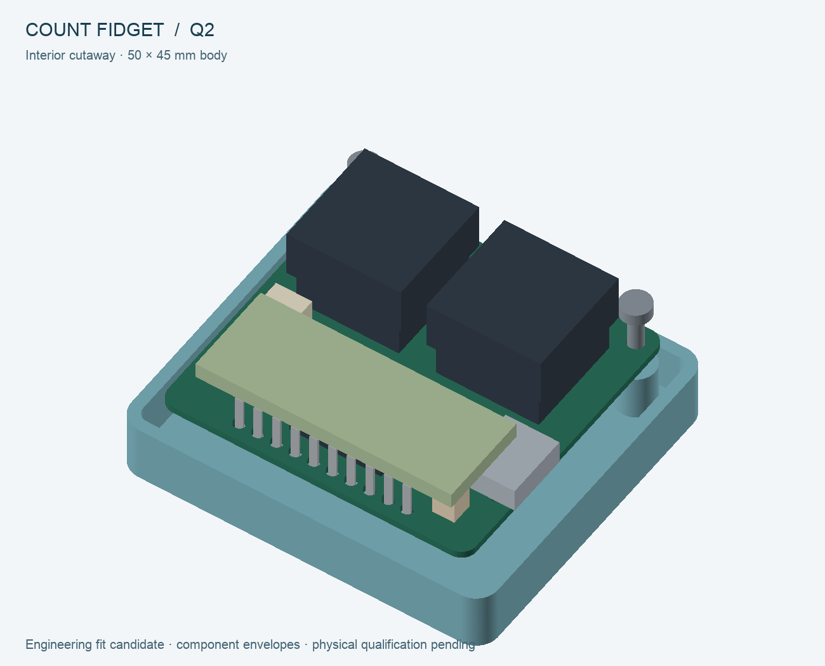
mechanical/q2/interior-Q2.png
