dudgeon/count-fidget/mechanical/q5/base-Q5.stl

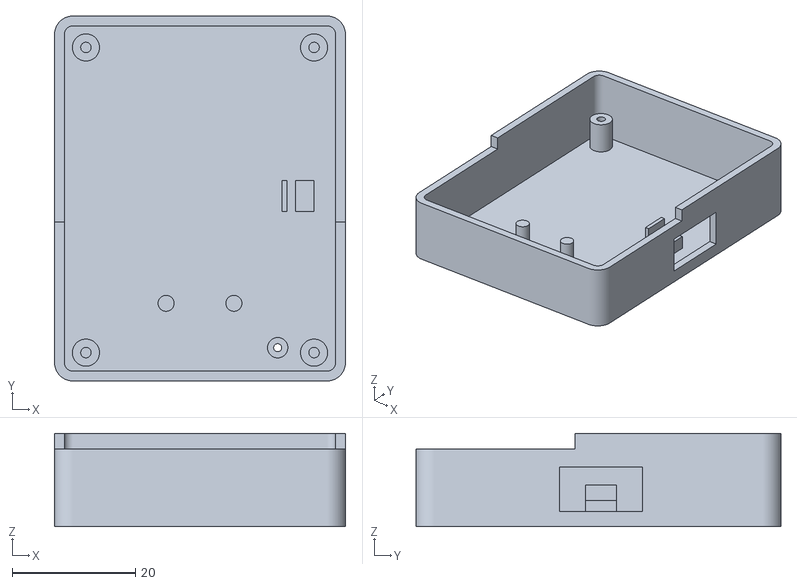
[picture p27: CAD file, 2026-09-26]
mechanical/q5/base-Q5.stl
47.2 x 59.2 x 15.1
