dudgeon/count-fidget/mechanical/q3/lid-front-Q3.stl

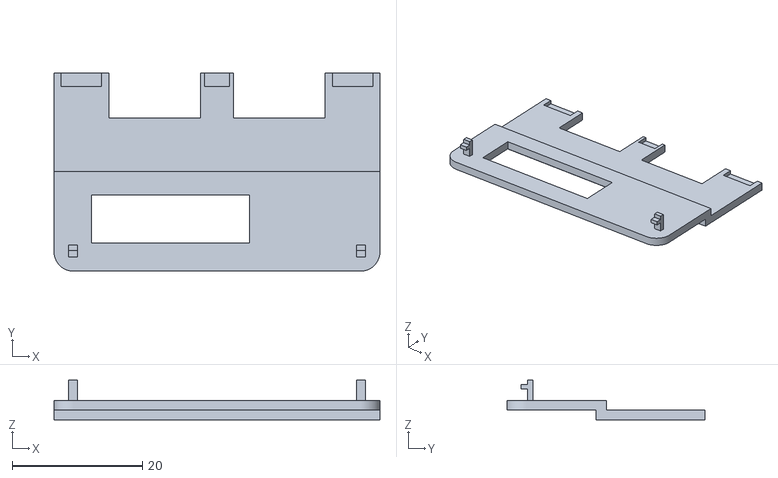
[picture p28: CAD file, 2026-09-25]
mechanical/q3/lid-front-Q3.stl
50.0 x 30.4 x 6.10
