dudgeon/count-fidget/mechanical/q4/base-Q4.stl

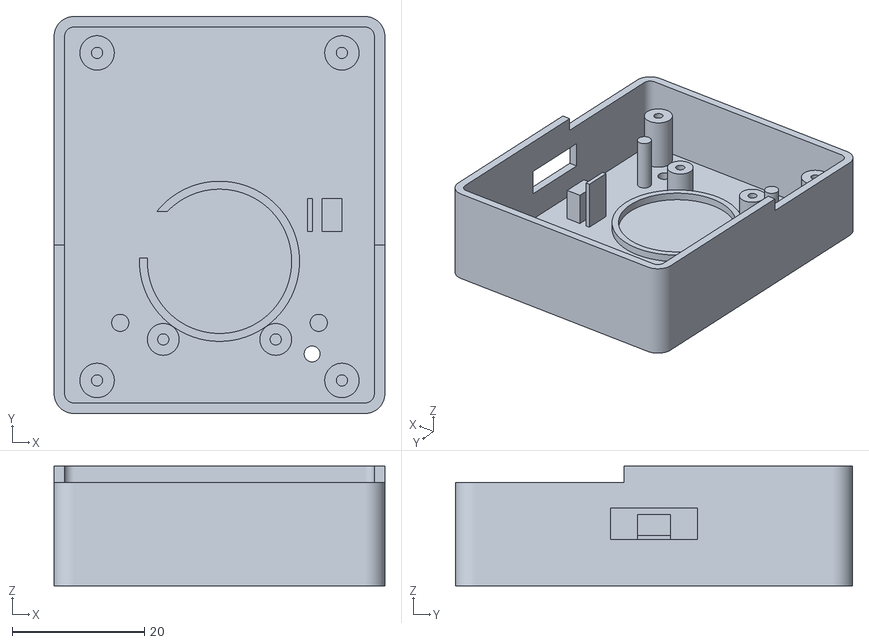
[picture p29: CAD file, 2026-09-25]
mechanical/q4/base-Q4.stl
50.0 x 60.0 x 18.1
