dudgeon/count-fidget/mechanical/q5/lid-rear-Q5.stl

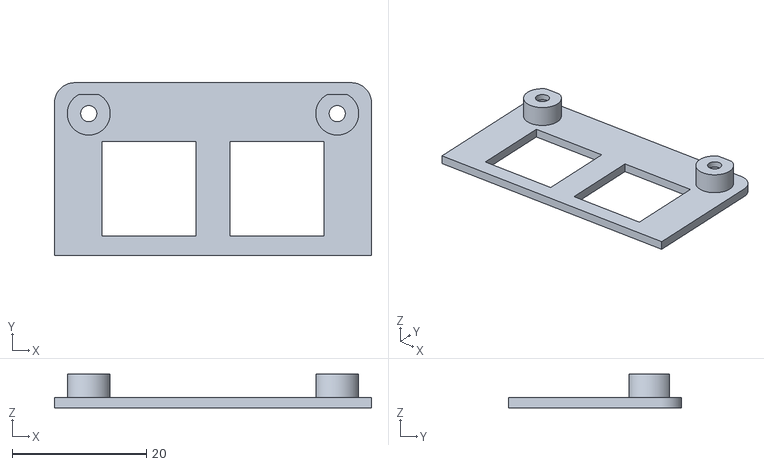
[picture p30: CAD file, 2026-09-26]
mechanical/q5/lid-rear-Q5.stl
47.2 x 25.7 x 5.00
