dudgeon/count-fidget/mechanical/q5/tolerance-coupon-Q5.stl

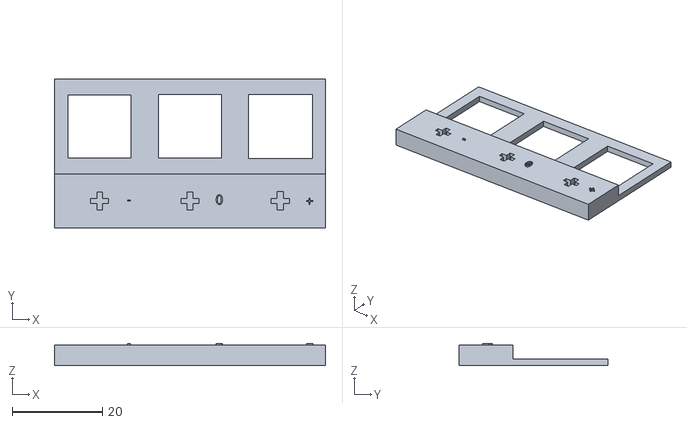
[picture p31: CAD file, 2026-09-26]
mechanical/q5/tolerance-coupon-Q5.stl
60.0 x 33.0 x 4.90
