dudgeon/count-fidget/mechanical/assembled-cad.png

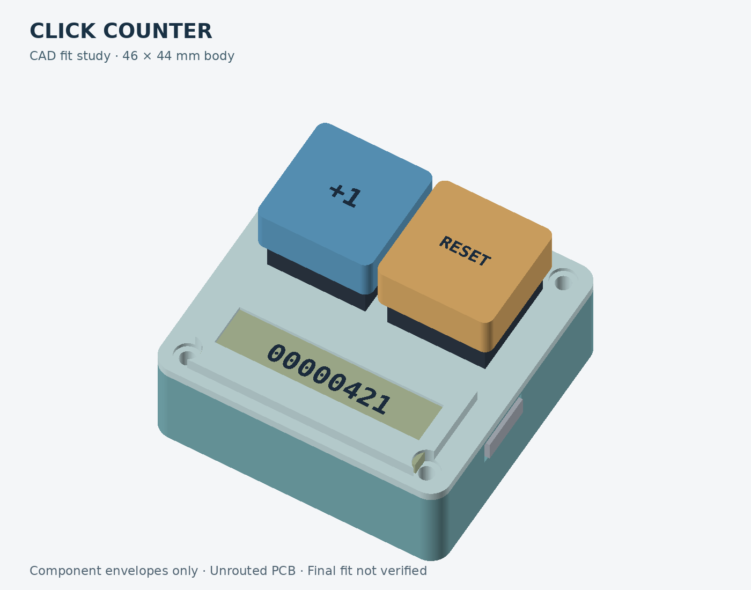
mechanical/assembled-cad.png
