dudgeon/count-fidget/mechanical/q2/assembled-Q2.png

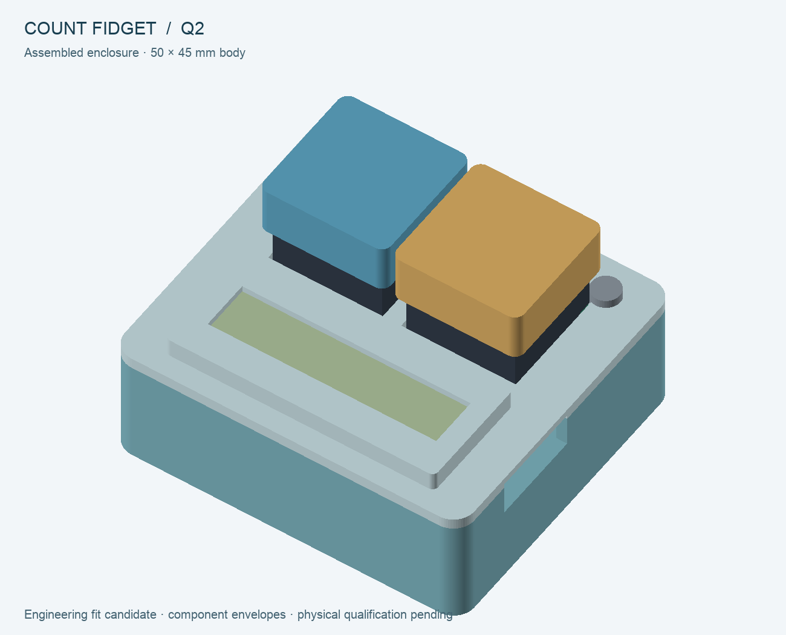
mechanical/q2/assembled-Q2.png
