dudgeon/count-fidget/mechanical/q3/assembled-Q3.png

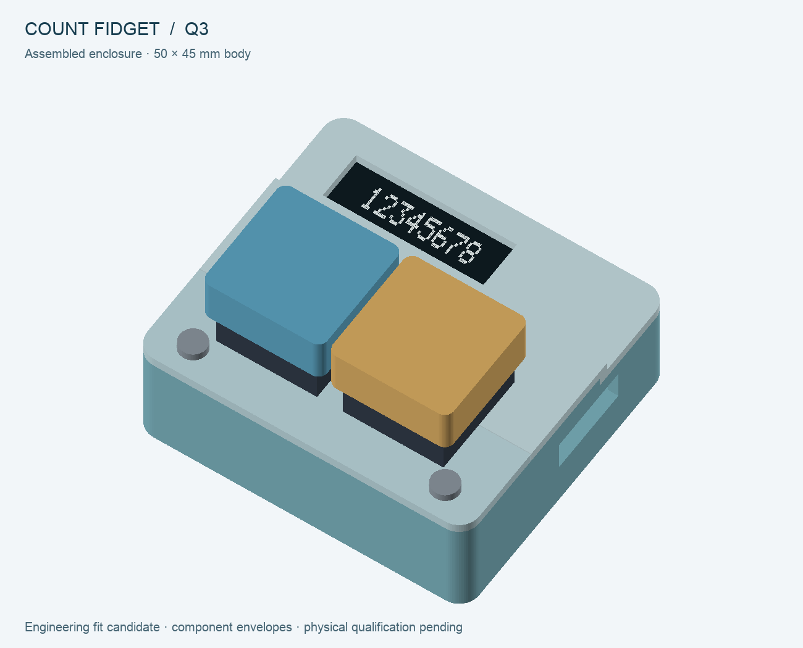
mechanical/q3/assembled-Q3.png
