dudgeon/count-fidget/procurement/assembly-bottom.png

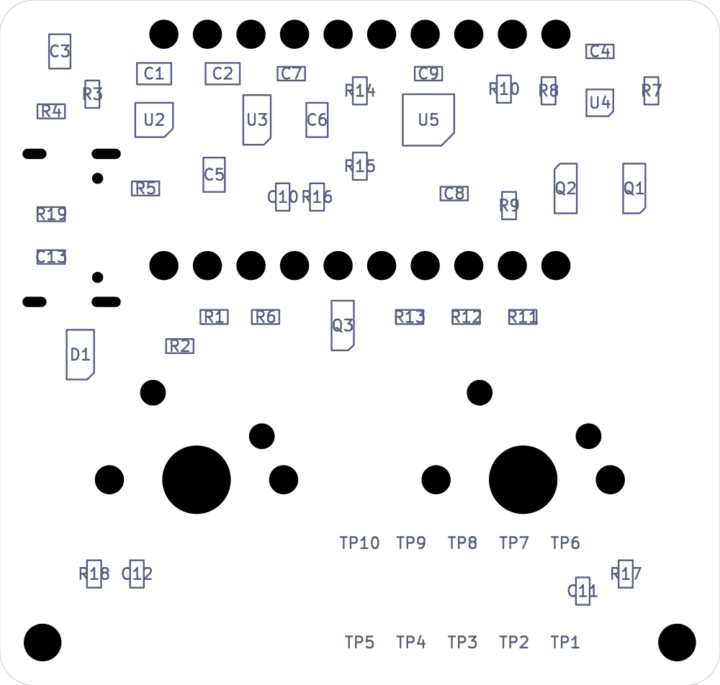
procurement/assembly-bottom.png
