dudgeon/count-fidget/procurement/assembly-top.png

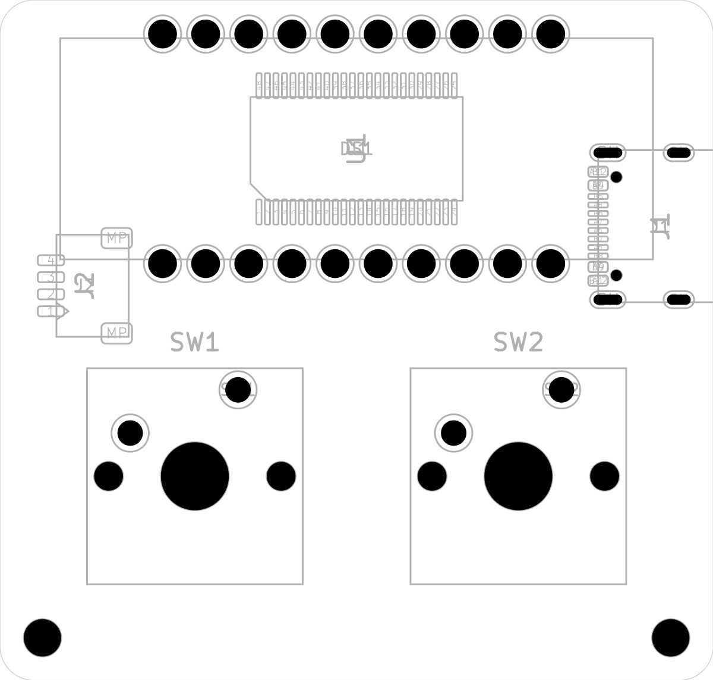
procurement/assembly-top.png
