dudgeon/count-fidget/firmware/q5-stm32/app.h

#ifndef Q5_APP_H
#define Q5_APP_H
#include "input.h"
#include "journal.h"
typedef struct {
    Counter counter;
    InputState input;
    Journal journal;
    bool storage_failed;
    uint32_t failed_revision;
} App;
/* raw_keys are INPUT_* levels at the end of boot; held keys are not presses. */
void app_init(App *a,const NvHal *hal,uint32_t now,uint8_t raw_keys);
/* The COUNT press that switched the board on counts once, unless the saved
 * count is uncertain (ERR), when increments remain frozen. */
void app_wake_press(App *a,uint32_t now);
void app_input(App *a,InputResult result,const InputSample *sample);
void app_service(App *a,const NvHal *hal,uint32_t now,bool power_good);
bool app_fault(const App *a);
bool app_settled(const App *a);
/* An idle fault is not a persistence acknowledgement. Backend quiescence and
 * display/ADC/input shutdown must additionally be checked by the target. */
bool app_can_idle(const App *a);
void app_storage_error(App *a);
#endif
