dudgeon/count-fidget/scripts/export_q5.py

"""Export Q5 engineering review files from current, saved native validation.

No uploads, quotation changes, purchases or manufacturing release are performed.
The factory list contains every jlc_smt placement (81 in Q5, all on the bottom,
including the two MX hot-swap sockets). Two quotation variants are exported:
  A: JLC SMT only; the user solders DS1 and its separate seven-pin header (14 joints);
  B: JLC SMT plus JLC through-hole assembly of DS1 and the header (no home soldering).
In both, the user presses the two loose clicky switches into the printed key plate and
the sockets, fits four M2 x 6 screws and inserts the user-supplied LIR2032 cell.
"""
import argparse
from collections import Counter, defaultdict
import csv
import hashlib
import json
import math
from pathlib import Path
import re
import shutil
import subprocess
import sys
import tempfile
import zipfile
import xml.etree.ElementTree as ET

ROOT = Path(__file__).resolve().parents[1]
DEST = ROOT / 'procurement/q5'
BOARD = ROOT / 'electronics/q5/click-counter-Q5.kicad_pcb'
MODEL = ROOT / 'electronics/q5/netlist-Q5.json'
VALIDATION = ROOT / 'verification/q5-validation.json'
STOCK = DEST / 'stock.json'
HARDWARE = DEST / 'hardware-bom.json'
MANIFEST = DEST / 'export-manifest-Q5.json'
GERBER_SUFFIXES = {
    'F_Cu.gtl', 'B_Cu.gbl', 'F_Mask.gts', 'B_Mask.gbs',
    'F_Silkscreen.gto', 'B_Silkscreen.gbo', 'F_Paste.gtp', 'B_Paste.gbp',
    'Edge_Cuts.gm1', 'PTH.drl', 'NPTH.drl', 'job.gbrjob',
}
EXPORT_NAMES = {
    'BOM-PCBA-Q5.csv', 'BOM-JLCPCB-Q5.csv', 'BOM-Q5.csv',
    'OFFBOARD-items-Q5.csv', 'HOME-COMPLETION-Q5.csv', 'SEPARATE-HARDWARE-Q5.csv', 'LOOSE-PARTS-Q5.csv',
    'CPL-JLCPCB-Q5.csv', 'BOM-JLCPCB-Q5-FULL-ASSEMBLY.csv', 'CPL-JLCPCB-Q5-FULL-ASSEMBLY.csv', 'placements-KiCad-Q5.csv',
    'assembly-top-Q5.svg', 'assembly-bottom-Q5.svg',
    'click-counter-Q5-Gerbers.zip', 'drill-report-Q5.txt', 'REVIEW-EXPORTS-Q5.md',
} | {'gerbers/click-counter-Q5-' + suffix for suffix in GERBER_SUFFIXES}
BOM_HEADER = [
    'Comment', 'Designator', 'Footprint', 'Quantity', 'Manufacturer',
    'Manufacturer Part Number', 'LCSC Part #', 'Assembly Role', 'Side',
    'Qualification', 'Notes',
]
JLC_HEADER = ['Comment', 'Designator', 'Footprint', 'LCSC Part #']
CPL_HEADER = ['Designator', 'Mid X', 'Mid Y', 'Layer', 'Rotation']
HOME_HEADER = BOM_HEADER + [
    'Retail Source', 'Observed UTC', 'Retail Stock', 'Minimum Order',
    'Order Multiple', 'Quantity for 10 (this reference)', 'Retail Order Group',
    'Retail Group Screening Quantity for 10 (shown once per MPN)',
    'Solder Joints', 'Assembly Sequence',
]


def require(condition, message):
    # Export guards must remain active even if Python is invoked with -O.
    if not condition:
        raise ValueError(message)


def digest(path):
    return hashlib.sha256(path.read_bytes()).hexdigest()


def ref_key(ref):
    match = re.fullmatch(r'([A-Z]+)(\d+)', ref)
    return (match[1], int(match[2])) if match else (ref, 0)


def write_csv(path, header, rows):
    with path.open('w', newline='', encoding='utf-8') as stream:
        writer = csv.writer(stream, lineterminator='\n')
        writer.writerow(header)
        writer.writerows(rows)


def read_csv(directory, name):
    with (directory / name).open(newline='', encoding='utf-8') as stream:
        reader = csv.DictReader(stream)
        return reader.fieldnames, list(reader)


def check_csv(directory, name, header, expected):
    fields, actual = read_csv(directory, name)
    require(fields == header, f'{name}: unexpected column mapping')
    wanted = [dict(zip(header, map(str, row))) for row in expected]
    require(actual == wanted, f'{name}: exact rows, identities, quantities or ordering differ')


def groups(parts):
    result = defaultdict(list)
    for part in parts:
        result[(part['mpn'], part['lcsc'])].append(part)
    return result


EXPECTED = dict(references=96, fitted=82, smt=81, home=1, features=14, types=42)
SCREW = dict(mpn='PA2X6nie', lcsc='C357360', manufacturer='Shuntian', quantity=4,
             description='M2 x 6 cross pan-head self-tapping screw (nickel)')
DS1_FOOTPRINT = ROOT / 'electronics/q5/CountFidgetQ5.pretty/HS96L01W4S03_Module_7Pin.kicad_mod'


def selected_parts(model):
    parts = model['parts']
    require(len(parts) == len({p['ref'] for p in parts}) == EXPECTED['references'], 'Unexpected native reference count')
    require(model['layers'] == 2 and model['board_mm'] == [42, 54, 1.6], 'Wrong Q5 board stack or outline')
    require(model.get('hardware_tested') is False and model.get('manufacturing_released') is False,
            'Model must preserve unqualified engineering status')
    require(Counter(p.get('assembly') for p in parts) ==
            {'jlc_smt': EXPECTED['smt'], 'home_through_hole': EXPECTED['home'], 'pcb_feature': EXPECTED['features']}, 'Assembly-role counts differ')
    fitted = sorted((p for p in parts if p['assembly'] != 'pcb_feature'), key=lambda p: ref_key(p['ref']))
    smt = [p for p in fitted if p['assembly'] == 'jlc_smt']
    home = [p for p in fitted if p['assembly'] == 'home_through_hole']
    require({p['ref'] for p in home} == {'DS1'}, 'Home completion reference set differs')
    require([(q['ref'], q['mpn'], q['lcsc']) for q in model.get('loose_parts', [])] ==
            [('K1', 'CPG151101D13', 'C49234235'), ('K2', 'CPG151101D13', 'C49234235')], 'Loose switch contract differs')
    require(all(p['side'] == 'bottom' for p in smt) and all(p['side'] == 'top' for p in home),
            'Single-sided (bottom) factory SMT contract changed')
    require(len(groups(fitted)) == len({p['mpn'] for p in fitted}) == EXPECTED['types'],
            'Expected exact fitted identities with one catalog code each')
    require(len({p['lcsc'] for p in fitted}) == EXPECTED['types'], 'Catalog code aliases distinct selected MPNs')
    require(all(p['mpn'] and p['manufacturer'] and re.fullmatch(r'C\d+', p['lcsc'])
                and p['footprint'].startswith('CountFidgetQ5:') for p in fitted), 'Missing exact identity or Q5 footprint')
    return fitted, smt, home


def check_retail(entry, refs, mpn, code, quantity):
    require(entry['references'] == sorted(refs), 'Retail references differ')
    require((entry['mpn'], entry['lcsc_part'], entry['quantity_per_board']) == (mpn, code, quantity),
            'Retail exact identity or quantity differs')
    require(entry['source'] == f'https://www.lcsc.com/product-detail/{code}.html' and entry['observed_at'],
            'Retail observation source missing')
    need = quantity * 10
    spares = max(2, math.ceil(need / 10))
    minimum, multiple = entry['minimum_order'], entry['order_multiple']
    require(isinstance(minimum, int) and isinstance(multiple, int) and minimum > 0 and multiple > 0,
            'Retail minimum/order multiple missing')
    rounded = math.ceil(max(need + spares, minimum) / multiple) * multiple
    require(entry['quantity_for_10'] == need and entry['screening_spares'] == spares and
            entry['rounded_screening_quantity'] == rounded, 'Retail screening quantity differs')
    require(entry['passes_retail_stock_screen'] is True and entry['in_stock'] >= rounded,
            'Insufficient observed loose-parts retail stock')


def fitted_identity_digest(model):
    fields = ('ref', 'mpn', 'lcsc', 'manufacturer', 'assembly')
    identities = [{field: p[field] for field in fields} for p in sorted(selected_parts(model)[0], key=lambda p: p['ref'])]
    return hashlib.sha256(json.dumps(identities, sort_keys=True, separators=(',', ':')).encode()).hexdigest()


def validate_sources(model, stock, hardware, model_hash):
    fitted, smt, home = selected_parts(model)
    plan = stock['screening_plan']
    require(plan['boards'] == 10 and plan['final_bom_screen_complete'] is True,
            'Complete ten-board stock screen required')
    require(plan['final_model_sha256'] == model_hash and plan.get('native_layout_binding_pending') is False,
            'Stock screen model binding is stale or layout binding pending')
    require(plan['fitted_identity_sha256'] == fitted_identity_digest(model), 'Stock identity digest differs')
    require(plan['fitted_positions'] == EXPECTED['fitted'] and plan['exact_fitted_types'] == EXPECTED['types'] and
            plan['assembly_role_positions'] == {'jlc_smt': EXPECTED['smt'], 'home_through_hole': EXPECTED['home'], 'pcb_feature': EXPECTED['features']},
            'Stock screen counts differ from current model')
    screen = stock['fitted_bom_screen']
    by_key = {(s['mpn'], s['jlc_part']): s for s in screen}
    require(len(by_key) == len(screen) == EXPECTED['types'] and set(by_key) == set(groups(fitted)),
            'Stock screen exact MPN/catalog identity set differs')
    selected_observations = []
    for key, matching in groups(fitted).items():
        row = by_key[key]
        quantity = len(matching)
        need = quantity * 10
        spares = max(2, math.ceil(need / 10))
        require(row['references'] == sorted(p['ref'] for p in matching) and row['fitted_per_board'] == quantity
                and row['assembly_roles'] == dict(Counter(p['assembly'] for p in matching)),
                f'Stock references, quantity or assembly role differs: {key[0]}')
        require((row['quantity_for_10'], row['screening_attrition'], row['screening_required_quantity']) ==
                (need, spares, need + spares), f'Stock screening quantity differs: {key[0]}')
        require(row['minimum_order'] >= 1 and row['available_order_quantity'] >=
                max(need + spares, row['minimum_order']) and row['passes_stock_screen'] is True,
                f'Insufficient observed orderable stock: {key[0]}')
        observations = [o for o in stock['observations'] if (o['mpn'], o['jlc_part'], o['observed_at']) ==
                        (*key, row['observed_at']) and o['available_order_quantity'] == row['available_order_quantity']
                        and o['minimum_order'] == row['minimum_order']]
        require(len(observations) == 1, f'Stock screen lacks exact catalog observation: {key[0]}')
        observation = observations[0]
        require(observation['source'] == f'https://jlcpcb.com/partdetail/{key[1]}', 'Unexpected stock source')
        selected_observations.append(observation)
    items = hardware['items']
    require(len(items) == 1, 'Expected one separately accounted OLED header')
    header = items[0]
    require((header['hardware_id'], header['mpn'], header['jlc_part'], header['quantity_per_board'],
             header['manufacturer'], header['solder_joints_per_assembly']) ==
            ('DS1-INTERPOSER', 'PZ254V-11-07P', 'C492406', 1, 'XFCN', 14), 'Separate header contract differs')
    separate = stock['separate_hardware_screen']
    require(len(separate) == 1 and separate[0]['mpn'] == header['mpn'] and
            separate[0]['jlc_part'] == header['jlc_part'] and separate[0]['quantity_for_10'] == 10 and
            separate[0]['screening_required_quantity'] == 12 and separate[0]['passes_stock_screen'] is True,
            'Separate header screen differs')
    retail = {(r['mpn'], r['lcsc_part']): r for r in stock['retail_home_parts']}
    expected_retail = set(groups(home)) | {(header['mpn'], header['jlc_part']), ('CPG151101D13', 'C49234235'),
                                           (SCREW['mpn'], SCREW['lcsc'])}
    require(len(retail) == len(stock['retail_home_parts']) == 4 and set(retail) == expected_retail,
            'Retail screen must cover the home display, header, loose switches and screws')
    for key, matching in groups(home).items():
        check_retail(retail[key], [p['ref'] for p in matching], *key, len(matching))
    check_retail(retail[(header['mpn'], header['jlc_part'])], ['DS1-INTERPOSER'],
                 header['mpn'], header['jlc_part'], 1)
    check_retail(retail[('CPG151101D13', 'C49234235')], ['K1', 'K2'], 'CPG151101D13', 'C49234235', 2)
    check_retail(retail[(SCREW['mpn'], SCREW['lcsc'])], ['SCREW1', 'SCREW2', 'SCREW3', 'SCREW4'],
                 SCREW['mpn'], SCREW['lcsc'], 4)
    tht = stock['variant_b_jlc_through_hole_screen']
    require(len(tht) == 1 and (tht[0]['mpn'], tht[0]['jlc_part'], tht[0]['references']) == ('HS96L01W4S03', 'C5139758', ['DS1'])
            and tht[0]['passes_stock_screen'] is True, 'Variant B JLC display screen missing or failing')
    return {'model_references': EXPECTED['references'], 'fitted_references': EXPECTED['fitted'], 'distinct_exact_mpns': EXPECTED['types'],
            'jlc_smt_references': EXPECTED['smt'], 'jlc_smt_exact_mpns': len(groups(smt)),
            'home_through_hole_references': ['DS1'], 'loose_switches': ['K1', 'K2'], 'screws_per_board': 4,
            'separate_header_quantity_per_board': 1, 'screened_boards': 10,
            'minimum_observed_jlc_stock': min((s['available_order_quantity'], s['mpn']) for s in screen),
            'catalog_observation_range_utc': [min(o['observed_at'] for o in selected_observations),
                                            max(o['observed_at'] for o in selected_observations)],
            'stock_is_unreserved_observation_not_qualification': True}


def bom_row(part):
    return [part['value'], part['ref'], part['footprint'], 1, part['manufacturer'], part['mpn'],
            part['lcsc'], part['assembly'], part['side'], 'Engineering candidate; physically unqualified', part['notes']]


def table_rows(model, stock, hardware):
    fitted, smt, home = selected_parts(model)
    pcb = [bom_row(part) for part in fitted]
    jlc = [[p['mpn'], p['ref'], p['footprint'], p['lcsc']] for p in smt]
    header = hardware['items'][0]
    separate = [[header['description'], header['hardware_id'], 'SEPARATE_HARDWARE', header['quantity_per_board'],
                 header['manufacturer'], header['mpn'], header['jlc_part'], 'home_header_interposer', '',
                 'Catalog screened; stack/solder fit unqualified',
                 'One header at DS1; no separate placement. Fourteen joints: seven module and seven host. '
                 'Loose header inclusion with module is unconfirmed; account once. ' + header['assembly_status']]]
    loose = [['Clicky MX switch, plate mount (COUNT / POWER)', 'K1', 'LOOSE_PART', 1, 'HanElectricity', 'CPG151101D13', 'C49234235',
              'user_presses_into_plate_and_SW1_socket', 'top', 'Catalog screened; retention in the printed plate/socket unqualified',
              'Clip into the rear key plate, then press the plate and switches into the hot-swap sockets. No soldering.'],
             ['Clicky MX switch, plate mount (RESET COUNT)', 'K2', 'LOOSE_PART', 1, 'HanElectricity', 'CPG151101D13', 'C49234235',
              'user_presses_into_plate_and_SW2_socket', 'top', 'Catalog screened; retention in the printed plate/socket unqualified',
              'Clip into the rear key plate, then press the plate and switches into the hot-swap sockets. No soldering.'],
             [SCREW['description'], 'SCREW1-SCREW4', 'LOOSE_PART', SCREW['quantity'], SCREW['manufacturer'], SCREW['mpn'], SCREW['lcsc'],
              'user_fits_enclosure', '', 'Catalog screened; thread strength in printed bosses unqualified',
              'Through the lid-boss floor and PCB mounting holes into 1.7 mm base pilots. LCSC retail (not a JLC placement).']]
    offboard = [
        ['LIR2032 rechargeable Li-ion coin cell (user supplied)', 'BAT1', 'OFFBOARD', 1, 'USER_SUPPLIED', 'LIR2032', '',
         'user_inserts_into_BT1', '', 'Consumable; exact cell brand and holder contact resistance unqualified',
         'Insert into the vendor-soldered BT1 holder with USB connected (USB-first). Rechargeable LIR2032 only: never a '
         'primary CR2032 or 3 V ML2032. No soldering to the cell. Not a JLC/LCSC assembly part.'],
    ]
    retail = {(r['mpn'], r['lcsc_part']): r for r in stock['retail_home_parts']}
    home_rows = []
    shown_retail_groups = set()
    for part in home:
        r = retail[(part['mpn'], part['lcsc'])]
        sequence = ('Variant A only: solder the separate seven-pin header to module and host (front cover removed); '
                    '14 joints, trim to the mechanical envelope. Variant B: JLC through-hole assembly.')
        key = (part['mpn'], part['lcsc'])
        grouped_quantity = r['rounded_screening_quantity'] if key not in shown_retail_groups else ''
        shown_retail_groups.add(key)
        home_rows.append(bom_row(part) + [r['source'], r['observed_at'], r['in_stock'], r['minimum_order'],
                         r['order_multiple'], 10, ','.join(r['references']), grouped_quantity,
                         14, sequence])
    full = jlc + [[p['mpn'], p['ref'], p['footprint'], p['lcsc']] for p in home] + \
        [[header['mpn'], 'DS1H', 'PinHeader_1x07_P2.54mm (stacked under DS1)', header['jlc_part']]]
    return {
        'BOM-PCBA-Q5.csv': (BOM_HEADER, pcb),
        'BOM-JLCPCB-Q5.csv': (JLC_HEADER, jlc),
        'BOM-JLCPCB-Q5-FULL-ASSEMBLY.csv': (JLC_HEADER, full),
        'HOME-COMPLETION-Q5.csv': (HOME_HEADER, home_rows),
        'SEPARATE-HARDWARE-Q5.csv': (BOM_HEADER, separate),
        'LOOSE-PARTS-Q5.csv': (BOM_HEADER, loose),
        'OFFBOARD-items-Q5.csv': (BOM_HEADER, offboard),
        'BOM-Q5.csv': (BOM_HEADER, pcb + separate + loose + offboard),
    }


def write_tables(directory, model, stock, hardware):
    for name, (header, rows) in table_rows(model, stock, hardware).items():
        write_csv(directory / name, header, rows)


def native_positions(directory, model):
    fitted, _, _ = selected_parts(model)
    parts = {p['ref']: p for p in fitted}
    fields, data = read_csv(directory, 'placements-KiCad-Q5.csv')
    require(fields == ['Ref', 'Val', 'Package', 'PosX', 'PosY', 'Rot', 'Side'], 'Unexpected native placement columns')
    require(len(data) == len({r['Ref'] for r in data}) == EXPECTED['fitted'] and {r['Ref'] for r in data} == set(parts),
            'Native placements must contain every fitted reference exactly once')
    for row in data:
        part = parts[row['Ref']]
        require(abs(float(row['PosX']) - part['x']) < 1e-6 and abs(float(row['PosY']) + part['y']) < 1e-6,
                f'Native placement coordinate differs: {part["ref"]}')
        require(abs((float(row['Rot']) - part['rotation'] + 180) % 360 - 180) < 1e-6 and row['Side'] == part['side'],
                f'Native placement side or rotation differs: {part["ref"]}')
        require(row['Package'] == part['footprint'].split(':', 1)[1], f'Native placement footprint differs: {part["ref"]}')
    return data


def cpl_rows(positions, model, full=False):
    _, smt, home = selected_parts(model)
    refs = {p['ref'] for p in smt} | ({p['ref'] for p in home} if full else set())
    rows = [[r['Ref'], r['PosX'] + 'mm', r['PosY'] + 'mm', r['Side'].title(), r['Rot']]
            for r in sorted(positions, key=lambda r: ref_key(r['Ref'])) if r['Ref'] in refs]
    if full:
        # The stacked header sits on DS1's seven host holes: its centre is the pad-row centroid.
        pads = [tuple(map(float, m)) for m in re.findall(r'\(pad "\d" thru_hole \w+ \(at (-?[\d.]+) (-?[\d.]+)', DS1_FOOTPRINT.read_text())]
        require(len(pads) == 7, 'DS1 footprint pad row not found')
        ds1 = next(r for r in positions if r['Ref'] == 'DS1')
        require(float(ds1['Rot']) % 360 == 0, 'DS1 header position assumes an unrotated module')
        cx = float(ds1['PosX']) + sum(x for x, _ in pads) / 7; cy = float(ds1['PosY']) - sum(y for _, y in pads) / 7
        rows.append(['DS1H', f'{cx:.4f}mm', f'{cy:.4f}mm', 'Top', '0'])
    return rows


def deterministic_zip(directory):
    with zipfile.ZipFile(directory / 'click-counter-Q5-Gerbers.zip', 'w', zipfile.ZIP_DEFLATED, compresslevel=9) as archive:
        for path in sorted((directory / 'gerbers').iterdir()):
            require(path.is_file() and not path.is_symlink(), 'Unexpected fabrication entry')
            info = zipfile.ZipInfo(path.name, date_time=(1980, 1, 1, 0, 0, 0))
            info.compress_type = zipfile.ZIP_DEFLATED
            info.external_attr = 0o100644 << 16
            archive.writestr(info, path.read_bytes(), compresslevel=9)


def validate_exports(directory, model, stock, hardware):
    for name, (header, rows) in table_rows(model, stock, hardware).items():
        check_csv(directory, name, header, rows)
    positions = native_positions(directory, model)
    cpl = cpl_rows(positions, model)
    require(len(cpl) == EXPECTED['smt'], 'Factory CPL count differs')
    check_csv(directory, 'CPL-JLCPCB-Q5.csv', CPL_HEADER, cpl)
    full = cpl_rows(positions, model, full=True)
    require(len(full) == EXPECTED['smt'] + 2 and {r[0] for r in full} - {r[0] for r in cpl} == {'DS1', 'DS1H'},
            'Full-assembly CPL must add exactly DS1 and its header')
    check_csv(directory, 'CPL-JLCPCB-Q5-FULL-ASSEMBLY.csv', CPL_HEADER, full)
    fabrication = directory / 'gerbers'
    expected = {'click-counter-Q5-' + suffix for suffix in GERBER_SUFFIXES}
    require({p.name for p in fabrication.iterdir()} == expected, 'Missing/unexpected fabrication file or inner copper layer')
    job = json.loads((fabrication / 'click-counter-Q5-job.gbrjob').read_text())
    require(job['GeneralSpecs']['LayerNumber'] == 2 and job['GeneralSpecs']['BoardThickness'] == 1.6 and
            job['GeneralSpecs']['ProjectId']['Name'] == 'click-counter-Q5', 'Wrong Gerber project/stack')
    require({x['Name'] for x in job['MaterialStackup'] if x['Type'] == 'Copper'} == {'F.Cu', 'B.Cu'},
            'Gerber job copper stack differs')
    attributes = job['FilesAttributes']
    require(len(attributes) == 9 and {x['Path'] for x in attributes} == expected -
            {'click-counter-Q5-' + s for s in ('PTH.drl', 'NPTH.drl', 'job.gbrjob')}, 'Gerber job file set differs')
    require({x['FileFunction'] for x in attributes if x['FileFunction'].startswith('Copper,')} ==
            {'Copper,L1,Top', 'Copper,L2,Bot'}, 'Gerber copper functions differ')
    geometry = r'(?:D01|D03|G36|G37)\*'
    require(not re.search(geometry, (fabrication / 'click-counter-Q5-F_Paste.gtp').read_text()),
            'Top paste must be empty: the only top-side part is the through-hole display')
    require(re.search(geometry, (fabrication / 'click-counter-Q5-B_Paste.gbp').read_text()),
            'Bottom SMT paste geometry missing')
    for layer in ('F_Cu.gtl', 'B_Cu.gbl', 'Edge_Cuts.gm1'):
        require(re.search(geometry, (fabrication / ('click-counter-Q5-' + layer)).read_text()), 'Empty native geometry: ' + layer)
    with zipfile.ZipFile(directory / 'click-counter-Q5-Gerbers.zip') as archive:
        require(len(archive.namelist()) == len(expected) and set(archive.namelist()) == expected and
                archive.testzip() is None, 'Gerber ZIP members/corruption differ')
        require(all(archive.read(name) == (fabrication / name).read_bytes() for name in expected),
                'Gerber ZIP bytes differ from native exports')
    for side in ('top', 'bottom'):
        svg = ET.parse(directory / f'assembly-{side}-Q5.svg').getroot()
        require(svg.tag == '{http://www.w3.org/2000/svg}svg' and
                any(node.tag.rsplit('}', 1)[-1] in {'path', 'polyline', 'polygon', 'circle', 'rect'}
                    for node in svg.iter()), 'Empty or malformed assembly SVG')
    actual_files = {p.relative_to(directory).as_posix() for p in directory.rglob('*') if p.is_file()}
    require(actual_files == EXPORT_NAMES, 'Unexpected export product set')
    for path in directory.rglob('*'):
        if path.is_file() and path.suffix != '.zip':
            data = path.read_text(encoding='utf-8')
            require(not re.search(r'/Users/|/private/|file://|(?:[A-Z]:\\Users\\)', data),
                    f'Private local path in public export: {path.name}')
    return {'engineering_pcb_bom_rows': EXPECTED['fitted'], 'engineering_complete_bom_rows': EXPECTED['fitted'] + 1 + 3 + 1,
            'jlc_smt_bom_and_cpl_rows': EXPECTED['smt'], 'full_assembly_bom_and_cpl_rows': EXPECTED['smt'] + 2,
            'native_placement_rows': EXPECTED['fitted'], 'home_completion_rows': 1, 'loose_part_rows': 3,
            'separate_header_rows': 1, 'home_solder_joints_per_board_variant_a': 14, 'home_solder_joints_per_board_variant_b': 0,
            'offboard_rows': 1, 'offboard_user_supplied_cell_only': True,
            'copper_layers': 2, 'gerber_and_drill_files': len(expected), 'top_paste_geometry': False,
            'bottom_paste_geometry': True, 'archive_members_equal_native_exports': True,
            'full_board_simulation_or_hardware_qualification': False}


def saved_validation():
    # No --kicad-cli: the verifier checks the saved, source-bound native evidence;
    # this exporter never creates a new native-validation claim for an unrouted board.
    subprocess.run([sys.executable, '-B', str(ROOT / 'scripts/verify_q5.py')], check=True, cwd=ROOT)
    result = json.loads(VALIDATION.read_text())
    require(result['status'] == 'PASS_NATIVE_DESIGN_CHECKS_ONLY' and result['hardware_tested'] is False and
            result['manufacturing_released'] is False, 'Current saved native validation is required')
    return result


def input_hashes(validation):
    paths = {BOARD, MODEL, VALIDATION, STOCK, HARDWARE, Path(__file__).resolve()}
    for mapping in ('inputs_sha256', 'reports_sha256'):
        for name, expected in validation[mapping].items():
            path = (ROOT / name).resolve()
            require(path.is_relative_to(ROOT) and not Path(name).is_absolute(), 'Non-public validation source path')
            require(digest(path) == expected, 'Changed native source or report: ' + name)
            paths.add(path)
    return {path.relative_to(ROOT).as_posix(): digest(path) for path in sorted(paths)}


def review_readme():
    return '''# Q5 fabrication and assembly exports

Engineering outputs for JLCPCB quotation. The hardware has not been physically
qualified. A quote is not an order: no purchase or manufacturing release is authorized.

Board: 42 x 54 mm, 2 layers, 1.6 mm FR-4, 1 oz, ENIG, green mask / white silk.
All factory SMT is on the BOTTOM side (single-sided assembly).

Two quotation variants:

| Variant | BOM | CPL | Who solders what |
|---|---|---|---|
| A | `BOM-JLCPCB-Q5.csv` (81 placements) | `CPL-JLCPCB-Q5.csv` | JLC: all 81 SMT parts. User: DS1 display on its 7-pin header (14 joints) |
| B | `BOM-JLCPCB-Q5-FULL-ASSEMBLY.csv` (83 placements) | `CPL-JLCPCB-Q5-FULL-ASSEMBLY.csv` | JLC: all SMT plus through-hole DS1 (C5139758) stacked on header DS1H (C492406), module PCB 2.5 mm above the host, pins trimmed <= 1 mm |

Both variants: the two clicky switches (K1/K2, C49234235) clip into the printed key
plate and press into the vendor-placed hot-swap sockets SW1/SW2 (no soldering); four
M2 x 6 self-tapping screws (C357360) close the printed enclosure; the user inserts a
rechargeable LIR2032 (never a primary CR2032). See `LOOSE-PARTS-Q5.csv`,
`HOME-COMPLETION-Q5.csv`, `SEPARATE-HARDWARE-Q5.csv` and `OFFBOARD-items-Q5.csv`.

Placement review items for the JLC DFM preview (bottom side, KiCad rotations, no
manufacturer correction applied): polarity/pin 1 of U1-U8, Q1-Q5, D1-D4, J1, the
BT1 holder (+ contact on pad 1 / CELL_P, marked + on the silkscreen) and the two
hot-swap sockets (pads beside the 3.0 mm switch-pin holes).

`BOM-PCBA-Q5.csv` / `placements-KiCad-Q5.csv` describe all 82 fitted parts. Stock
counts are timestamped, unreserved public catalogue observations in `stock.json`.
See `export-manifest-Q5.json` for exact source/output hashes and checks.
'''


def export(args, output):
    # Remove a previous success marker before attempting a replacement. Failed
    # exports leave no current success marker; all new products are staged first.
    MANIFEST.unlink(missing_ok=True)
    validation = saved_validation()
    initial = input_hashes(validation)
    model, stock, hardware = (json.loads(path.read_text()) for path in (MODEL, STOCK, HARDWARE))
    source_checks = validate_sources(model, stock, hardware, digest(MODEL))
    cli_path = Path(args.kicad_cli).resolve()
    require(cli_path.is_file(), 'KiCad CLI does not exist')
    require(digest(cli_path) == validation['tool_sha256'], 'Export/native-validation KiCad executables differ')
    tool = {'version': subprocess.check_output([str(cli_path), 'version'], text=True).strip(), 'sha256': digest(cli_path)}
    require(tool['version'].startswith('10.'), 'KiCad 10 required')
    output.mkdir(exist_ok=True, parents=True)
    write_tables(output, model, stock, hardware)
    commands = []

    def cli(*arguments):
        command = [str(cli_path), 'pcb', 'export', *map(str, arguments), str(BOARD)]
        subprocess.run(command, check=True, cwd=ROOT)
        commands.append(['<kicad-cli>'] + [v.replace(str(output), '<output>').replace(str(ROOT) + '/', '') for v in command[1:]])

    fabrication = output / 'gerbers'
    fabrication.mkdir()
    cli('gerbers', '--output', fabrication, '--layers',
        'F.Cu,B.Cu,F.Mask,B.Mask,F.SilkS,B.SilkS,F.Paste,B.Paste,Edge.Cuts', '--subtract-soldermask')
    cli('drill', '--output', fabrication, '--excellon-separate-th', '--excellon-units', 'mm',
        '--excellon-oval-format', 'route', '--generate-report', '--report-path', output / 'drill-report-Q5.txt')
    cli('pos', '--output', output / 'placements-KiCad-Q5.csv', '--format', 'csv', '--units', 'mm', '--side', 'both', '--exclude-dnp')
    positions = native_positions(output, model)
    write_csv(output / 'CPL-JLCPCB-Q5.csv', CPL_HEADER, cpl_rows(positions, model))
    write_csv(output / 'CPL-JLCPCB-Q5-FULL-ASSEMBLY.csv', CPL_HEADER, cpl_rows(positions, model, full=True))
    for side, layer in [('top', 'F'), ('bottom', 'B')]:
        options = ['svg', '--output', output / f'assembly-{side}-Q5.svg', '--mode-single', '--layers',
                   f'{layer}.Cu,{layer}.Fab,{layer}.SilkS,Edge.Cuts', '--fit-page-to-board',
                   '--exclude-drawing-sheet', '--sketch-pads-on-fab-layers']
        if side == 'bottom':
            options.append('--mirror')
        cli(*options)
    deterministic_zip(output)
    (output / 'REVIEW-EXPORTS-Q5.md').write_text(review_readme(), encoding='utf-8')
    checks = validate_exports(output, model, stock, hardware)
    require(input_hashes(validation) == initial, 'Design, stock or validation changed during export')
    require(saved_validation() == validation, 'Saved validation changed during export')
    products = [p for p in sorted(output.rglob('*')) if p.is_file()]
    manifest = {
        'schema_version': 1, 'revision': 'Q5 engineering review candidate', 'status': 'PASS_REVIEW_EXPORT_CHECKS_ONLY',
        'hardware_tested': False, 'manufacturing_released': False,
        'quote_authorization': 'JLCPCB quotes for variants A and B only (user, 25 Sep 2026); no order, payment or release', 'source_board_sha256': initial[BOARD.relative_to(ROOT).as_posix()],
        'inputs_sha256': initial, 'kicad_cli': tool, 'commands': commands,
        'source_checks': source_checks, 'export_checks': checks,
        'files': {str((DEST / p.relative_to(output)).relative_to(ROOT)):
                  {'bytes': p.stat().st_size, 'sha256': digest(p)} for p in products},
    }
    DEST.mkdir(exist_ok=True, parents=True)
    if (DEST / 'gerbers').exists():
        shutil.rmtree(DEST / 'gerbers')
    for source in products:
        target = DEST / source.relative_to(output)
        target.parent.mkdir(exist_ok=True, parents=True)
        shutil.copyfile(source, target)
    for name, entry in manifest['files'].items():
        require(digest(ROOT / name) == entry['sha256'] and (ROOT / name).stat().st_size == entry['bytes'],
                'Published output copy differs: ' + name)
    require(input_hashes(validation) == initial, 'Sources changed while publishing staged exports')
    MANIFEST.write_text(json.dumps(manifest, indent=2, sort_keys=True) + '\n', encoding='utf-8')
    print('Q5 exports checked: 82 board parts; variant A 81 SMT BOM/CPL (DS1 home-soldered); variant B 83 placements incl. DS1 + header THT. Hardware unqualified.')


def main():
    parser = argparse.ArgumentParser(description=__doc__)
    parser.add_argument('--kicad-cli', required=True)
    args = parser.parse_args()
    try:
        with tempfile.TemporaryDirectory(prefix='count-fidget-q5-export-') as folder:
            export(args, Path(folder))
    except (ValueError, KeyError, OSError, subprocess.CalledProcessError, zipfile.BadZipFile, ET.ParseError) as error:
        print('FAIL: ' + str(error), file=sys.stderr)
        return 1
    return 0


if __name__ == '__main__':
    sys.exit(main())
