dudgeon/count-fidget/scripts/test_firmware_q5.py

"""Compile/run the production Q5 portable code against deterministic fault models."""
import argparse
import hashlib
import json
import shutil
import struct
from pathlib import Path
import subprocess
import tempfile
ROOT=Path(__file__).resolve().parents[1]
SOURCE=ROOT/'firmware/q5-stm32'
GROUPS={'behavior':['test_behavior.c','counter.c','input.c','journal.c','app.c'],
        'battery':['test_battery.c','battery.c'],
        'fram':['test_fram.c','fram.c','journal.c'],
        'oled':['test_oled.c','oled.c'],'rail':['test_rail.c','rail.c']}
def record(p):
    data=p.read_bytes();return {'bytes':len(data),'sha256':hashlib.sha256(data).hexdigest()}
def run_tests(sanitize=False,cc='clang'):
    outputs={}
    source_files=[p for p in SOURCE.glob('*') if p.suffix in ('.c','.h')]
    before={p.name:record(p) for p in source_files}
    with tempfile.TemporaryDirectory(prefix='count-fidget-q5-tests-') as td:
        for name,files in GROUPS.items():
            exe=Path(td)/name
            command=[cc,'-std=c11','-O2','-Wall','-Wextra','-Werror','-Wno-misleading-indentation','-I'+str(SOURCE)]
            if sanitize:command+=['-fsanitize=undefined','-fno-sanitize-recover=all','-fno-omit-frame-pointer','-DTEAR_STEP=257']
            subprocess.run(command+[str(SOURCE/f) for f in files]+['-o',str(exe)],check=True,capture_output=True,text=True)
            outputs[name]=subprocess.check_output([str(exe)],text=True,timeout=180)
    if before!={p.name:record(p) for p in source_files}:raise ValueError('Source changed during test run')
    return outputs
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
